wgd-modular/utf-8-samplified/firmware/mattel/mattel.h

const uint8_t BD[923] PROGMEM =          //BD_Samples:923
{
128,125,124,125,122,122,121,121,115,142,193,202,205,209,211,215,217,221,224,228,230,230,230,229,228,228,226,228,219,192,166,142,119,101,83,68,57,48,38,33,28,25,21,21,20,19,18,18,14,11,9,5,0,0,0,0,0,0,2,5,6,6,7,9,10,11,11,11,11,11,11,13,13,13,13,13,11,13,10,11,11,10,9,10,10,9,10,9,9,9,10,9,10,10,10,10,10,11,14,20,28,33,40,48,55,63,71,76,82,86,90,92,97,100,102,105,109,112,116,120,124,130,134,138,144,151,156,161,167,173,178,185,190,196,201,206,212,217,223,228,233,236,241,247,250,254,254,254,254,254,254,254,254,254,254,254,254,254,254,254,254,254,254,254,254,254,254,254,254,254,254,254,254,254,254,254,254,254,254,254,254,254,254,254,254,254,254,254,254,254,254,254,254,254,254,254,254,253,252,252,250,248,247,247,244,244,243,241,241,239,239,238,231,226,221,216,211,206,201,196,191,186,181,176,171,166,161,156,152,148,143,139,135,130,128,122,119,115,111,107,103,100,97,93,91,87,85,82,78,77,73,71,68,66,63,61,58,57,53,50,49,47,44,42,40,39,37,33,31,30,28,28,25,24,20,20,19,18,15,14,14,13,11,10,9,9,7,6,6,6,5,5,5,4,4,4,2,2,4,4,4,5,5,6,6,7,9,10,11,11,14,16,16,18,20,21,23,25,26,29,31,34,34,38,39,42,44,45,48,50,52,54,55,59,62,62,66,67,68,71,71,73,76,78,78,81,82,83,86,87,88,90,92,92,95,95,97,98,100,102,101,102,105,106,106,109,109,110,111,112,114,115,116,116,117,120,121,121,122,122,124,125,128,128,128,129,129,130,133,132,134,135,137,137,139,139,140,140,142,143,144,144,145,147,148,148,149,149,152,153,153,154,154,154,157,157,158,158,159,159,159,161,161,161,162,162,163,164,164,164,164,164,166,166,166,166,166,167,167,167,167,167,167,168,168,168,167,168,168,167,168,167,167,167,167,167,167,166,167,168,167,166,167,167,167,167,167,166,167,167,167,167,166,167,167,167,167,166,168,168,168,168,168,168,168,168,169,169,171,169,171,169,169,172,172,171,171,171,171,171,171,171,171,172,171,171,171,171,172,169,171,169,169,169,168,168,168,168,169,168,167,167,166,167,166,166,164,166,164,163,163,163,162,162,162,159,159,159,158,158,158,157,157,156,157,154,154,154,153,152,153,153,152,151,151,151,149,149,149,148,148,148,147,148,147,147,145,145,144,144,144,144,143,142,142,142,140,140,140,139,138,139,138,137,134,135,134,134,133,133,132,130,129,129,128,128,125,128,125,124,122,122,121,121,120,120,119,119,115,116,115,115,114,111,111,110,110,109,109,107,107,106,106,106,105,105,103,103,102,102,101,102,101,100,100,100,100,98,98,100,98,97,98,97,97,97,97,97,97,97,97,97,97,97,97,97,97,97,97,97,97,96,98,96,98,96,97,96,96,97,96,96,96,97,96,97,97,97,97,96,97,97,97,96,96,96,97,97,97,97,97,98,97,97,98,97,97,98,97,98,98,98,98,100,100,100,100,101,102,102,101,102,101,103,103,103,103,105,106,106,107,107,109,110,111,110,111,111,112,114,115,115,115,115,117,116,119,119,120,120,120,121,121,122,121,124,124,124,124,125,125,125,128,125,128,128,129,129,128,128,128,129,130,130,130,130,130,132,130,132,133,132,132,133,132,133,133,133,133,134,134,133,134,134,135,135,134,135,135,135,137,137,137,138,138,138,138,138,138,140,140,139,140,140,142,142,142,142,142,143,144,144,144,144,144,145,144,147,145,145,147,145,145,145,145,145,147,147,147,145,147,145,145,145,147,145,145,144,144,145,144,144,143,144,142,143,143,142,142,142,142,142,142,140,140,139,139,138,139,137,138,138,138,138,137,137,137,137,137,137,135,135,135,135,135,134,134,134,133,134,134,134,134,134,134,134,133,134,133,133,134,133,134,133,134,133,133,132,133,133,132,133,132,132,132,132,130,130,130,130,129,129,130,129,129,129,128,128,128,128,128,125,125,
};

const uint8_t SD[1824] PROGMEM =          //SD_SAMPLES:1824
{
128,132,128,132,132,132,128,142,103,4,34,0,9,29,49,49,73,78,108,98,128,128,128,167,147,157,157,211,177,162,142,226,152,172,137,182,172,132,162,152,216,172,147,73,152,108,98,201,123,147,123,118,182,147,152,93,103,211,73,172,152,132,201,172,192,152,157,147,113,103,157,73,147,128,128,157,73,123,132,132,108,137,142,123,201,103,167,113,152,162,142,137,137,177,128,88,118,157,83,98,108,128,78,162,118,123,78,83,157,93,167,68,64,132,88,93,88,147,128,132,14,177,98,54,172,64,162,142,128,113,147,152,44,123,103,68,162,108,64,118,113,118,118,113,128,118,78,98,128,73,113,73,142,93,162,108,93,64,73,137,59,88,73,132,88,147,108,118,172,103,142,88,167,88,113,142,128,142,128,123,103,73,108,132,108,103,44,157,93,54,167,83,157,128,98,157,137,137,118,167,152,68,98,162,34,206,113,103,128,132,167,157,172,78,108,162,98,147,113,103,177,68,182,128,187,132,98,108,123,118,142,113,113,167,118,167,152,113,172,128,78,187,123,137,147,147,162,157,157,128,152,132,147,132,177,152,137,88,152,118,98,172,113,162,108,147,137,157,118,132,137,128,103,157,59,157,167,68,177,98,177,172,167,113,118,172,108,128,147,137,162,137,123,147,132,132,142,128,147,132,123,132,157,132,123,118,152,113,93,137,103,108,142,113,108,152,147,123,128,128,152,113,177,128,137,128,142,103,123,167,93,132,142,147,128,98,142,137,108,142,103,172,137,113,118,152,128,132,142,132,142,123,132,132,123,142,128,128,132,147,137,142,123,128,128,132,157,142,132,118,108,93,128,113,108,147,98,123,128,123,128,128,152,118,152,123,162,113,137,167,142,128,152,142,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
};

const uint8_t HT[2424] PROGMEM =          //HT_SAMPLES:2424
{
129,128,132,132,135,133,135,133,136,131,142,107,35,22,6,2,0,5,10,21,34,54,74,95,116,138,158,177,194,209,218,224,228,229,228,225,220,215,206,197,185,172,160,147,136,125,114,106,100,95,93,92,96,105,115,128,142,156,171,185,198,209,215,218,220,220,217,214,208,202,193,183,171,158,144,132,120,109,99,91,84,77,73,72,75,84,92,104,116,130,143,155,167,175,180,183,183,183,178,174,168,160,152,140,128,115,102,89,78,68,59,51,44,41,38,36,38,46,55,66,79,92,104,117,130,142,150,156,159,161,159,157,153,148,142,135,125,115,103,93,83,73,64,58,51,47,44,42,43,43,49,59,70,83,96,110,124,136,148,159,168,172,176,176,175,171,166,160,153,146,137,126,115,105,94,85,77,71,65,61,58,57,57,58,62,71,81,93,106,120,132,146,158,169,179,186,190,192,191,189,185,180,174,167,159,150,138,128,119,109,102,95,88,84,80,79,79,79,80,86,94,105,116,129,141,153,166,176,187,196,202,205,205,205,201,196,191,184,176,167,157,146,136,124,115,107,99,92,87,82,80,79,79,80,82,87,97,107,118,131,142,153,165,175,184,192,197,200,200,198,195,190,185,177,170,161,151,141,131,121,112,104,97,92,87,84,82,82,81,82,85,89,98,108,118,129,141,152,161,171,180,187,193,196,196,195,191,187,180,173,166,158,148,138,127,118,109,101,94,87,81,78,75,75,74,74,76,78,83,91,100,111,121,131,142,152,161,168,176,182,185,186,185,183,177,173,166,159,153,144,134,125,115,107,100,93,87,83,79,77,76,76,77,78,81,84,91,99,109,120,130,140,149,158,166,174,180,185,187,187,185,182,177,171,166,158,151,142,134,124,115,107,100,93,88,84,81,79,78,78,79,81,82,84,90,98,106,115,125,136,144,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
,128,128,128,128,127,128,128,128,129,128,128,129,127,128,128,129,128,128,129,128,128,129,128,129,128,129,128,128,128,128,129,128,128,127,127,129,128,128,128,129,129,128,128,128,127,129,127,127,128,128,128,127,128,128,128,128,128,128,128,128,127,128,128,128,128,128,128,128,128,128,129,128,128,129,128,129,128,128,128,128,129,128,128,128,128,128,128,128,128,128,128,129,128,127,128,128,128,128,128,127,127,128,128,128,128,128,128,128,129,128,128,128,128,
};

const uint8_t HT3[2885] PROGMEM =          //HT3_SAMPLES:2885
{
128,123,118,114,109,104,100,95,91,86,82,76,76,85,96,108,122,135,152,168,185,201,215,230,243,250,255,255,255,253,251,246,241,234,229,223,216,210,205,200,196,192,189,188,187,187,187,187,188,188,189,190,191,189,188,186,182,179,174,170,164,159,153,147,140,134,127,122,116,111,105,101,97,94,92,88,86,84,83,83,81,82,81,81,81,80,80,79,79,77,77,77,78,80,82,86,90,94,98,102,105,109,114,117,119,123,126,128,131,133,136,138,138,141,142,143,144,144,145,145,145,144,144,143,140,138,136,134,131,128,126,123,121,118,116,113,110,109,107,104,102,101,98,97,95,94,91,88,86,83,80,78,74,72,70,67,64,63,61,59,59,57,55,54,54,53,53,52,53,53,53,55,54,55,57,58,58,61,63,63,66,67,69,70,73,76,77,79,80,83,86,89,94,100,104,111,117,122,129,134,141,146,152,157,162,167,172,176,179,184,187,190,192,195,197,200,202,203,204,205,206,207,206,206,206,205,204,201,200,197,195,193,191,189,186,184,181,179,176,174,171,169,166,163,162,160,157,153,150,147,144,141,136,133,130,126,125,121,118,115,113,110,110,108,105,103,103,101,100,99,98,97,97,97,96,95,95,95,94,95,94,94,94,94,94,95,95,95,96,96,96,97,98,99,99,101,103,107,110,115,119,123,127,132,137,141,144,148,153,157,160,164,167,169,172,175,177,179,181,183,184,186,188,189,190,191,191,193,193,193,193,193,192,192,190,188,187,186,184,181,179,176,175,171,169,166,163,160,157,155,151,147,145,141,137,134,130,125,122,118,114,111,107,105,101,99,95,93,90,88,86,84,83,80,78,78,75,74,73,72,72,71,70,70,69,69,69,68,70,69,70,70,70,71,72,72,73,75,77,77,80,81,83,83,85,89,92,96,101,105,111,116,121,126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
};

const uint8_t LT[1921] PROGMEM =          //LT_SAMPLES:1921
{
128,128,128,128,127,129,129,128,128,128,128,127,129,128,128,128,128,127,128,128,128,128,128,128,127,128,128,128,128,128,128,128,127,128,128,128,128,128,128,128,128,128,127,128,127,127,126,126,126,126,126,126,125,125,125,126,126,125,125,125,126,126,127,127,126,128,127,128,128,129,129,129,129,129,131,130,130,131,131,131,131,131,132,131,131,131,131,131,130,130,130,130,130,129,129,129,128,127,127,127,126,127,127,126,126,125,125,125,125,125,124,124,124,123,123,123,122,123,123,122,123,122,123,122,122,122,123,123,124,124,124,125,126,126,127,128,129,130,131,131,132,133,134,135,135,136,137,137,138,139,138,139,139,140,140,140,139,139,139,139,137,137,137,136,135,135,134,133,130,130,130,130,130,130,128,128,125,123,121,119,118,118,117,118,118,118,118,118,116,115,113,112,111,110,111,111,111,112,113,114,114,114,114,114,114,115,116,119,120,122,124,125,126,127,127,129,129,133,136,140,143,148,148,150,145,142,132,127,66,29,17,3,3,5,18,31,52,72,94,113,131,142,152,157,161,161,161,158,156,154,151,148,142,138,133,127,123,118,121,125,135,146,156,168,181,193,205,216,227,238,247,253,255,255,253,249,243,235,228,219,211,202,193,185,176,168,161,155,147,139,129,119,110,102,94,89,83,79,76,73,71,71,71,71,72,74,80,91,102,115,129,142,154,166,177,187,196,202,209,212,210,206,199,190,182,171,161,151,141,131,123,113,106,99,92,87,82,76,69,62,55,48,42,38,33,29,27,24,22,22,21,20,21,21,21,22,28,36,47,57,69,81,93,106,116,127,138,146,154,163,169,173,174,173,169,166,161,155,149,144,137,133,127,122,118,115,112,110,107,10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
};
