wgd-modular/utf-8-samplified/firmware/cavetechno/CH.h

#ifndef CH_H_
#define CH_H_
 
const uint16_t CHLen = 2347;

const uint8_t CH[2347] PROGMEM = {130, 125, 131, 125, 131, 128, 129, 120, 137,
120, 143, 112, 150, 109, 135, 159, 14, 190, 124, 104, 151, 158, 108, 147, 108,
162, 201, 82, 166, 103, 77, 75, 134, 67, 157, 85, 123, 183, 131, 191, 169, 174,
140, 154, 93, 163, 53, 89, 79, 55, 103, 106, 142, 145, 185, 123, 225, 156, 170,
180, 132, 112, 83, 57, 96, 94, 40, 150, 84, 135, 167, 171, 182, 191, 143, 170,
168, 70, 149, 87, 63, 75, 83, 89, 142, 116, 149, 188, 134, 182, 180, 161, 136,
136, 93, 106, 70, 92, 113, 76, 114, 127, 151, 152, 170, 161, 176, 133, 148, 144,
106, 117, 93, 93, 87, 95, 114, 152, 109, 147, 164, 143, 167, 152, 145, 145, 118,
98, 139, 82, 101, 116, 96, 116, 129, 136, 156, 155, 125, 171, 139, 135, 145,
127, 118, 108, 94, 113, 117, 100, 135, 123, 131, 138, 149, 152, 142, 136, 145,
133, 117, 129, 114, 116, 103, 108, 125, 122, 124, 147, 134, 123, 147, 138, 146,
137, 127, 132, 126, 102, 126, 128, 102, 130, 118, 126, 134, 126, 139, 144, 123,
140, 146, 127, 133, 123, 124, 116, 114, 120, 132, 118, 122, 129, 128, 133, 132,
146, 136, 131, 131, 136, 122, 123, 122, 121, 123, 112, 127, 132, 122, 123, 139,
125, 138, 137, 134, 141, 121, 125, 133, 119, 118, 133, 118, 120, 119, 124, 136,
128, 130, 141, 136, 128, 139, 131, 129, 121, 122, 127, 118, 119, 127, 125, 119,
130, 133, 139, 132, 134, 139, 128, 123, 130, 128, 122, 121, 118, 126, 119, 122,
135, 131, 127, 137, 135, 134, 134, 125, 134, 123, 119, 127, 125, 119, 124, 123,
126, 131, 127, 140, 134, 130, 132, 133, 126, 129, 125, 125, 123, 115, 127, 125,
125, 125, 134, 129, 136, 133, 136, 134, 121, 132, 128, 123, 123, 127, 122, 124,
118, 130, 133, 126, 134, 135, 131, 128, 134, 129, 133, 121, 127, 129, 119, 123,
127, 126, 123, 129, 129, 136, 128, 130, 134, 130, 126, 133, 130, 127, 125, 120,
129, 118, 125, 130, 127, 127, 130, 130, 132, 133, 129, 137, 127, 128, 129, 128,
122, 124, 123, 123, 126, 125, 132, 128, 128, 130, 135, 130, 134, 132, 131, 128,
120, 128, 123, 122, 124, 127, 123, 128, 127, 134, 132, 127, 135, 133, 129, 128,
130, 123, 125, 120, 128, 126, 123, 130, 129, 128, 128, 134, 132, 134, 126, 132,
128, 123, 126, 127, 125, 124, 126, 126, 132, 125, 132, 131, 128, 129, 132, 130,
128, 126, 125, 129, 121, 128, 129, 128, 125, 129, 127, 130, 129, 130, 134, 125,
129, 128, 128, 125, 127, 127, 128, 124, 127, 131, 125, 128, 128, 132, 128, 130,
129, 132, 126, 125, 130, 127, 126, 127, 129, 124, 125, 125, 131, 128, 127, 130,
131, 129, 128, 132, 128, 129, 125, 130, 126, 125, 127, 127, 126, 125, 129, 129,
130, 127, 132, 129, 128, 128, 131, 129, 127, 128, 125, 127, 123, 127, 127, 126,
127, 130, 130, 129, 130, 131, 132, 127, 130, 129, 127, 124, 126, 124, 124, 125,
127, 131, 126, 130, 131, 132, 129, 132, 131, 131, 125, 125, 127, 123, 124, 124,
127, 125, 129, 129, 133, 129, 131, 133, 131, 130, 128, 129, 124, 124, 122, 126,
124, 126, 128, 129, 129, 130, 133, 131, 132, 129, 132, 126, 126, 124, 125, 123,
123, 126, 127, 128, 128, 133, 130, 131, 131, 133, 130, 128, 127, 126, 124, 122,
126, 125, 126, 126, 130, 129, 130, 130, 132, 131, 129, 131, 128, 127, 124, 126,
126, 125, 125, 129, 128, 127, 129, 129, 131, 129, 130, 131, 130, 126, 128, 127,
125, 126, 126, 127, 126, 127, 129, 129, 127, 129, 131, 130, 130, 129, 129, 127,
126, 127, 127, 125, 127, 128, 127, 127, 127, 130, 130, 129, 130, 131, 127, 128,
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

#endif /* CH_H_ */
