wgd-modular/utf-8-samplified/firmware/cavetechno/CL.h

#ifndef CL_H_
#define CL_H_
 
const uint16_t CLLen = 2447;

const uint8_t CL[2447] PROGMEM = {128, 127, 128, 127, 128, 128, 128, 128, 128,
128, 127, 129, 127, 129, 125, 128, 125, 117, 126, 120, 138, 145, 122, 168, 167,
112, 88, 126, 138, 168, 156, 131, 111, 135, 168, 116, 171, 134, 49, 77, 177, 84,
89, 188, 175, 172, 140, 121, 114, 104, 74, 108, 117, 137, 154, 149, 132, 130,
134, 138, 135, 138, 128, 109, 98, 104, 130, 122, 104, 124, 133, 117, 149, 161,
158, 124, 121, 141, 123, 109, 124, 119, 107, 113, 127, 126, 138, 153, 126, 164,
157, 144, 112, 97, 121, 106, 111, 90, 103, 143, 144, 155, 169, 149, 136, 114,
101, 120, 112, 117, 123, 119, 133, 135, 152, 149, 146, 118, 113, 116, 114, 132,
121, 120, 119, 122, 126, 140, 141, 149, 146, 127, 116, 127, 133, 127, 105, 105,
102, 123, 143, 129, 141, 125, 137, 158, 145, 136, 143, 107, 85, 98, 122, 130,
141, 139, 148, 144, 126, 105, 133, 180, 67, 164, 179, 98, 153, 123, 108, 124,
146, 125, 119, 152, 114, 75, 170, 152, 94, 135, 142, 113, 128, 114, 133, 137,
112, 149, 144, 140, 132, 101, 118, 129, 91, 163, 103, 122, 160, 121, 146, 115,
116, 111, 133, 139, 154, 114, 106, 131, 167, 154, 129, 126, 68, 90, 106, 130,
175, 153, 139, 139, 131, 118, 99, 99, 111, 151, 159, 134, 97, 106, 122, 150,
159, 151, 154, 94, 92, 142, 156, 91, 102, 140, 107, 130, 143, 154, 146, 108, 97,
114, 143, 143, 153, 156, 134, 98, 100, 97, 112, 148, 131, 137, 136, 138, 131,
129, 129, 116, 127, 127, 136, 146, 126, 101, 108, 129, 143, 159, 137, 120, 108,
91, 137, 147, 131, 97, 130, 157, 114, 139, 127, 124, 148, 121, 130, 118, 93,
143, 141, 123, 120, 119, 131, 131, 133, 149, 129, 101, 113, 150, 138, 132, 141,
115, 77, 108, 146, 113, 166, 169, 115, 89, 135, 148, 135, 134, 115, 108, 125,
147, 116, 118, 142, 96, 124, 163, 117, 86, 175, 166, 78, 172, 118, 80, 169, 155,
46, 117, 164, 99, 162, 172, 93, 90, 156, 164, 134, 118, 134, 112, 106, 101, 125,
128, 124, 168, 179, 129, 80, 111, 157, 156, 109, 99, 112, 111, 121, 152, 158,
137, 122, 108, 125, 125, 123, 146, 139, 117, 130, 123, 94, 129, 152, 142, 145,
143, 109, 95, 125, 143, 145, 124, 140, 125, 122, 107, 94, 123, 125, 184, 150,
130, 126, 75, 94, 153, 179, 107, 102, 153, 130, 112, 108, 149, 162, 115, 129,
126, 89, 110, 130, 129, 133, 136, 170, 151, 122, 97, 93, 138, 123, 112, 133,
130, 140, 150, 135, 124, 137, 140, 106, 88, 114, 160, 128, 111, 151, 136, 122,
144, 113, 102, 156, 156, 122, 88, 107, 124, 125, 145, 153, 155, 129, 108, 140,
113, 103, 133, 112, 152, 125, 91, 164, 133, 125, 154, 102, 117, 135, 149, 109,
88, 132, 171, 156, 91, 147, 166, 106, 107, 77, 117, 167, 105, 152, 144, 91, 128,
158, 146, 142, 123, 94, 108, 119, 143, 159, 172, 132, 97, 103, 98, 115, 151,
157, 100, 96, 124, 157, 167, 115, 83, 112, 160, 171, 140, 122, 125, 89, 124,
136, 124, 139, 147, 124, 92, 117, 132, 140, 152, 146, 109, 126, 133, 123, 136,
110, 88, 116, 162, 160, 142, 135, 99, 94, 94, 135, 159, 158, 142, 96, 140, 146,
108, 98, 130, 148, 115, 109, 140, 166, 130, 106, 86, 107, 158, 158, 157, 129,
101, 90, 137, 168, 136, 87, 109, 133, 131, 134, 114, 135, 162, 164, 113, 89,
103, 136, 163, 154, 117, 76, 83, 118, 188, 178, 118, 103, 129, 164, 108, 100,
123, 130, 123, 136, 150, 118, 114, 143, 147, 104, 139, 142, 100, 122, 146, 114,
103, 170, 161, 99, 92, 118, 145, 141, 142, 132, 133, 144, 92, 103, 136, 136, 95,
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

#endif /* CL_H_ */
