wgd-modular/utf-8-samplified/firmware/dilectro/BD.h

#ifndef BD_H_
#define BD_H_
 
const uint16_t BDLen = 3332;

const uint8_t BD[3332] PROGMEM = {128, 128, 128, 58, 58, 82, 84, 85, 72, 62, 50,
42, 42, 61, 56, 56, 55, 60, 68, 79, 90, 102, 114, 126, 139, 150, 162, 172, 183,
192, 201, 209, 218, 225, 233, 238, 244, 247, 250, 252, 253, 253, 252, 251, 248,
245, 242, 238, 232, 227, 220, 212, 203, 194, 184, 173, 162, 150, 139, 130, 121,
114, 107, 101, 95, 90, 85, 81, 77, 73, 69, 66, 63, 60, 58, 56, 54, 52, 50, 49,
48, 47, 46, 45, 45, 45, 44, 44, 44, 44, 44, 45, 45, 46, 47, 48, 49, 50, 51, 53,
54, 56, 58, 59, 61, 64, 66, 68, 70, 73, 76, 78, 81, 84, 87, 90, 94, 97, 101,
105, 109, 113, 117, 121, 126, 130, 135, 139, 144, 149, 154, 158, 163, 168, 173,
178, 182, 187, 191, 196, 200, 204, 208, 212, 216, 220, 223, 226, 229, 232, 234,
236, 238, 240, 241, 243, 243, 244, 244, 244, 243, 243, 242, 241, 239, 237, 236,
234, 231, 229, 226, 223, 220, 217, 214, 211, 207, 204, 200, 196, 193, 189, 185,
181, 177, 173, 169, 165, 160, 156, 152, 148, 144, 140, 136, 131, 127, 123, 119,
115, 111, 108, 104, 100, 96, 93, 89, 86, 82, 79, 76, 73, 70, 67, 64, 61, 58, 56,
53, 51, 48, 46, 44, 42, 40, 38, 37, 35, 34, 32, 31, 30, 29, 28, 28, 27, 27, 26,
26, 26, 26, 26, 26, 27, 27, 28, 29, 29, 30, 32, 33, 34, 36, 37, 39, 40, 42, 44,
46, 48, 51, 53, 55, 58, 60, 63, 65, 68, 71, 74, 77, 80, 83, 86, 89, 92, 96, 99,
103, 106, 110, 113, 117, 121, 125, 129, 134, 138, 142, 147, 151, 155, 160, 164,
169, 173, 178, 182, 186, 191, 195, 199, 203, 207, 210, 214, 218, 221, 224, 227,
230, 233, 235, 237, 239, 241, 242, 243, 244, 245, 245, 245, 245, 244, 244, 243,
241, 240, 238, 236, 234, 231, 229, 226, 223, 220, 217, 214, 211, 207, 204, 200,
197, 193, 190, 186, 182, 178, 175, 171, 167, 163, 160, 156, 152, 148, 144, 141,
137, 133, 129, 126, 122, 119, 115, 112, 108, 105, 102, 98, 95, 92, 89, 86, 84,
81, 78, 76, 73, 71, 68, 66, 64, 62, 60, 58, 56, 55, 53, 52, 50, 49, 48, 47, 46,
45, 45, 44, 43, 43, 43, 43, 43, 43, 43, 43, 43, 44, 44, 45, 46, 47, 48, 49, 50,
51, 52, 54, 55, 57, 58, 60, 62, 64, 66, 68, 70, 72, 74, 76, 78, 80, 82, 85, 87,
89, 92, 94, 97, 99, 102, 105, 107, 110, 113, 115, 118, 121, 123, 126, 129, 132,
134, 137, 140, 143, 146, 149, 152, 155, 157, 160, 163, 166, 169, 172, 174, 177,
180, 182, 185, 187, 190, 192, 194, 196, 198, 200, 202, 203, 205, 206, 207, 208,
209, 210, 210, 211, 211, 211, 211, 210, 210, 209, 208, 207, 206, 205, 204, 202,
201, 199, 197, 196, 194, 192, 190, 188, 186, 184, 181, 179, 177, 175, 172, 170,
168, 165, 163, 161, 158, 156, 153, 151, 149, 146, 144, 141, 139, 136, 134, 132,
129, 127, 125, 122, 120, 118, 116, 114, 111, 109, 107, 105, 104, 102, 100, 98,
96, 95, 93, 91, 90, 88, 87, 85, 84, 83, 82, 81, 80, 79, 78, 77, 76, 75, 75, 74,
74, 73, 73, 72, 72, 72, 72, 72, 72, 72, 72, 72, 73, 73, 74, 74, 75, 75, 76, 77,
78, 79, 79, 80, 81, 83, 84, 85, 86, 87, 89, 90, 91, 93, 94, 96, 97, 99, 100,
102, 104, 105, 107, 109, 110, 112, 114, 116, 117, 119, 121, 123, 124, 126, 128,
130, 132, 133, 135, 137, 139, 140, 142, 144, 146, 147, 149, 151, 153, 154, 156,
158, 159, 161, 162, 164, 165, 167, 168, 170, 171, 172, 173, 174, 176, 176, 177,
178, 179, 180, 180, 181, 181, 181, 181, 182, 182, 182, 181, 181, 181, 180, 180,
179, 178, 178, 177, 176, 175, 174, 173, 172, 170, 169, 168, 167, 166, 164, 163,
162, 160, 159, 157, 156, 154, 153, 151, 150, 148, 147, 145, 144, 142, 140, 139,
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

#endif /* BD_H_ */
