wgd-modular/utf-8-samplified/firmware/dilectro/CR.h

#ifndef CR_H_
#define CR_H_
 
const uint16_t CRLen = 7156;

const uint8_t CR[7156] PROGMEM = {128, 127, 125, 125, 125, 122, 120, 119, 121,
120, 116, 116, 120, 125, 133, 140, 147, 152, 157, 158, 166, 215, 223, 186, 149,
110, 78, 52, 36, 30, 30, 34, 49, 74, 103, 135, 160, 179, 194, 206, 210, 216,
233, 215, 185, 153, 120, 91, 67, 52, 43, 42, 42, 77, 106, 117, 133, 145, 159,
167, 174, 174, 175, 190, 180, 158, 137, 116, 95, 76, 66, 64, 69, 74, 86, 103,
124, 145, 163, 177, 186, 189, 186, 179, 185, 189, 165, 134, 106, 82, 66, 56, 54,
59, 66, 79, 97, 117, 137, 155, 167, 174, 178, 178, 175, 178, 170, 153, 136, 119,
106, 95, 89, 86, 88, 90, 100, 119, 127, 134, 141, 146, 149, 150, 150, 148, 151,
149, 139, 130, 121, 113, 105, 101, 100, 102, 105, 110, 118, 127, 135, 143, 150,
154, 155, 154, 151, 152, 154, 146, 132, 119, 107, 98, 93, 92, 93, 97, 103, 112,
122, 133, 143, 149, 154, 156, 157, 155, 157, 153, 143, 133, 123, 114, 107, 103,
101, 102, 103, 109, 122, 128, 133, 137, 141, 143, 144, 144, 142, 144, 142, 136,
129, 123, 117, 112, 109, 108, 110, 112, 116, 121, 127, 133, 139, 143, 146, 147,
146, 144, 145, 146, 140, 131, 121, 113, 107, 104, 103, 104, 106, 111, 117, 124,
131, 138, 143, 145, 147, 147, 146, 147, 145, 138, 131, 124, 119, 114, 111, 110,
111, 111, 116, 124, 128, 131, 134, 136, 138, 138, 138, 137, 138, 137, 133, 129,
125, 121, 118, 116, 116, 117, 118, 120, 124, 127, 131, 135, 138, 140, 141, 140,
139, 139, 140, 136, 130, 123, 118, 114, 111, 110, 111, 113, 116, 120, 125, 130,
135, 139, 141, 142, 143, 142, 143, 141, 135, 130, 125, 121, 117, 115, 113, 114,
114, 118, 125, 128, 131, 133, 135, 136, 137, 137, 136, 137, 136, 132, 129, 125,
122, 118, 117, 116, 117, 118, 121, 124, 128, 131, 135, 138, 139, 140, 140, 138,
139, 140, 136, 130, 123, 118, 114, 112, 111, 112, 113, 116, 120, 125, 130, 135,
138, 141, 142, 142, 141, 142, 140, 135, 130, 125, 121, 117, 115, 114, 114, 115,
118, 125, 128, 131, 133, 135, 136, 137, 137, 136, 137, 136, 132, 129, 125, 122,
119, 117, 117, 117, 119, 121, 124, 128, 131, 135, 137, 139, 140, 139, 138, 139,
139, 136, 129, 124, 118, 115, 112, 111, 112, 114, 117, 121, 125, 130, 135, 138,
140, 141, 142, 141, 142, 140, 135, 130, 125, 121, 118, 115, 114, 115, 115, 119,
125, 128, 131, 133, 135, 136, 136, 136, 135, 137, 136, 132, 129, 125, 122, 119,
117, 117, 118, 119, 121, 124, 128, 131, 134, 137, 139, 139, 139, 138, 138, 139,
135, 129, 124, 119, 115, 113, 112, 113, 114, 117, 121, 125, 130, 135, 138, 140,
141, 141, 140, 141, 139, 135, 130, 125, 121, 118, 116, 115, 115, 116, 119, 125,
128, 130, 133, 134, 136, 136, 136, 135, 136, 135, 132, 129, 125, 122, 119, 118,
117, 118, 119, 121, 124, 128, 131, 134, 137, 138, 139, 139, 137, 138, 138, 135,
129, 124, 119, 115, 113, 113, 113, 115, 117, 121, 126, 130, 135, 137, 139, 141,
141, 140, 141, 139, 134, 130, 125, 122, 118, 116, 115, 116, 116, 119, 125, 128,
130, 132, 134, 135, 136, 136, 135, 136, 135, 132, 128, 125, 122, 120, 118, 118,
119, 120, 122, 124, 128, 131, 134, 136, 138, 139, 138, 137, 137, 138, 135, 129,
124, 119, 116, 114, 113, 114, 115, 118, 121, 126, 130, 134, 137, 139, 140, 140,
140, 140, 139, 134, 130, 125, 122, 118, 117, 116, 116, 117, 120, 125, 128, 130,
132, 134, 135, 136, 135, 135, 136, 135, 132, 128, 125, 123, 120, 118, 118, 119,
120, 122, 125, 128, 131, 134, 136, 138, 138, 138, 137, 137, 138, 135, 129, 124,
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

#endif /* CR_H_ */
