wgd-modular/utf-8-samplified/firmware/dilectro/OH.h

#ifndef OH_H_
#define OH_H_
 
const uint16_t OHLen = 3035;

const uint8_t OH[3035] PROGMEM = {129, 127, 129, 127, 129, 136, 125, 130, 125,
134, 122, 129, 126, 137, 116, 137, 127, 118, 141, 122, 130, 127, 131, 123, 133,
126, 132, 122, 138, 118, 133, 129, 130, 125, 124, 137, 119, 138, 121, 134, 123,
131, 125, 131, 130, 127, 121, 135, 131, 128, 129, 135, 131, 126, 144, 122, 135,
127, 133, 118, 135, 128, 119, 136, 126, 120, 138, 122, 126, 140, 124, 143, 124,
136, 117, 142, 124, 117, 135, 123, 121, 129, 128, 117, 133, 121, 134, 119, 129,
125, 137, 123, 133, 120, 131, 127, 118, 136, 112, 142, 117, 131, 128, 122, 128,
126, 122, 135, 119, 124, 123, 131, 126, 117, 142, 121, 132, 121, 131, 120, 135,
128, 120, 133, 121, 127, 129, 128, 126, 125, 133, 123, 132, 128, 123, 132, 120,
136, 123, 132, 129, 131, 132, 125, 128, 131, 125, 133, 117, 133, 134, 120, 136,
123, 128, 126, 126, 126, 130, 128, 132, 122, 141, 123, 134, 126, 130, 125, 129,
124, 128, 132, 120, 136, 121, 133, 121, 131, 125, 131, 119, 135, 115, 139, 124,
140, 118, 132, 129, 113, 142, 114, 137, 112, 141, 114, 137, 125, 132, 125, 131,
124, 133, 126, 127, 135, 117, 134, 123, 137, 119, 133, 122, 134, 118, 136, 123,
133, 126, 127, 131, 127, 129, 127, 128, 125, 134, 120, 134, 122, 132, 121, 134,
125, 129, 130, 129, 129, 128, 130, 126, 132, 126, 130, 127, 127, 129, 130, 124,
129, 126, 131, 126, 128, 127, 131, 126, 129, 126, 128, 131, 119, 138, 124, 126,
134, 124, 132, 127, 127, 128, 126, 131, 124, 129, 128, 128, 126, 127, 125, 134,
126, 129, 125, 129, 131, 125, 130, 125, 136, 117, 135, 126, 132, 126, 129, 127,
129, 128, 124, 136, 122, 132, 126, 134, 123, 133, 124, 132, 122, 137, 127, 125,
137, 118, 139, 118, 137, 126, 127, 132, 126, 129, 131, 125, 133, 124, 133, 130,
119, 137, 124, 134, 123, 133, 123, 133, 127, 126, 132, 125, 132, 128, 129, 128,
128, 129, 127, 128, 132, 120, 137, 124, 130, 126, 132, 129, 126, 133, 124, 130,
128, 130, 127, 130, 125, 133, 120, 135, 122, 133, 127, 127, 129, 126, 134, 124,
132, 127, 130, 125, 134, 122, 134, 126, 126, 129, 133, 122, 132, 130, 123, 130,
127, 133, 124, 131, 127, 127, 131, 127, 130, 129, 123, 133, 125, 132, 126, 131,
126, 129, 126, 131, 130, 125, 132, 127, 127, 128, 129, 127, 127, 129, 131, 121,
136, 123, 131, 127, 129, 127, 130, 127, 130, 126, 130, 129, 124, 134, 122, 132,
124, 131, 125, 130, 126, 130, 127, 128, 125, 133, 125, 128, 127, 128, 128, 123,
134, 124, 131, 124, 132, 125, 130, 127, 130, 124, 131, 126, 127, 130, 127, 128,
128, 128, 125, 134, 123, 132, 125, 131, 127, 129, 128, 127, 129, 128, 127, 128,
129, 126, 130, 128, 128, 128, 128, 128, 128, 126, 131, 124, 129, 128, 127, 128,
129, 128, 128, 128, 128, 128, 126, 131, 124, 131, 126, 127, 130, 125, 129, 127,
128, 129, 124, 131, 126, 127, 129, 126, 130, 126, 130, 126, 129, 128, 126, 129,
127, 127, 127, 129, 128, 124, 130, 128, 126, 128, 129, 126, 129, 128, 124, 132,
126, 129, 127, 128, 129, 126, 129, 127, 127, 130, 125, 128, 131, 123, 132, 124,
131, 126, 127, 129, 127, 129, 126, 129, 127, 130, 125, 130, 124, 133, 125, 128,
128, 129, 126, 130, 127, 124, 133, 123, 131, 127, 128, 126, 131, 125, 130, 128,
130, 125, 130, 129, 126, 128, 128, 128, 126, 132, 123, 134, 125, 129, 128, 127,
128, 127, 127, 131, 125, 127, 129, 128, 128, 128, 129, 126, 131, 126, 129, 126,
130, 125, 130, 128, 129, 126, 130, 126, 128, 130, 126, 128, 127, 130, 125, 131,
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

#endif /* OH_H_ */
