wgd-modular/utf-8-samplified/firmware/dilectro/RD.h

#ifndef RD_H_
#define RD_H_
 
const uint16_t RDLen = 4867;

const uint8_t RD[4867] PROGMEM = {127, 129, 127, 129, 127, 129, 126, 130, 126,
130, 125, 133, 118, 37, 36, 50, 55, 65, 64, 61, 54, 55, 59, 76, 77, 111, 199,
233, 241, 239, 227, 224, 218, 219, 217, 217, 215, 215, 212, 210, 207, 204, 201,
199, 197, 195, 194, 193, 192, 192, 192, 182, 167, 153, 140, 127, 115, 103, 91,
79, 70, 57, 44, 34, 22, 21, 26, 30, 33, 35, 37, 39, 40, 42, 44, 46, 49, 51, 53,
56, 57, 59, 59, 60, 69, 80, 89, 98, 106, 115, 124, 132, 140, 146, 155, 163, 170,
177, 182, 188, 193, 197, 201, 205, 208, 212, 214, 212, 209, 206, 204, 203, 201,
199, 198, 196, 192, 188, 183, 179, 174, 169, 163, 157, 151, 144, 138, 131, 123,
115, 108, 100, 93, 88, 81, 74, 69, 63, 59, 55, 52, 49, 47, 47, 50, 52, 54, 56,
58, 59, 60, 62, 67, 72, 77, 82, 87, 93, 98, 103, 109, 115, 120, 126, 132, 138,
142, 146, 153, 157, 162, 166, 170, 174, 178, 181, 184, 186, 189, 190, 192, 193,
193, 193, 194, 193, 194, 189, 182, 179, 176, 174, 171, 168, 164, 160, 156, 151,
146, 142, 137, 131, 126, 120, 115, 109, 104, 99, 95, 89, 84, 80, 77, 74, 71, 69,
67, 66, 66, 66, 66, 67, 69, 71, 73, 76, 78, 82, 85, 89, 93, 97, 102, 106, 110,
115, 120, 125, 129, 134, 138, 141, 146, 151, 154, 158, 161, 164, 167, 170, 172,
174, 176, 178, 179, 180, 180, 181, 180, 180, 180, 179, 177, 176, 174, 172, 170,
167, 164, 161, 157, 153, 150, 145, 141, 137, 132, 128, 123, 119, 114, 109, 105,
101, 98, 93, 89, 86, 83, 81, 79, 78, 76, 75, 75, 75, 76, 77, 78, 80, 82, 84, 86,
89, 92, 95, 99, 102, 106, 109, 113, 117, 121, 125, 128, 132, 136, 138, 143, 146,
149, 152, 155, 158, 160, 163, 165, 166, 168, 170, 171, 172, 172, 173, 173, 173,
172, 171, 170, 169, 168, 166, 165, 163, 160, 158, 155, 152, 149, 146, 142, 139,
136, 132, 128, 124, 120, 117, 113, 109, 106, 103, 101, 96, 94, 92, 90, 88, 86,
85, 84, 84, 84, 84, 84, 85, 86, 87, 89, 91, 93, 95, 97, 100, 103, 106, 109, 112,
115, 118, 121, 125, 128, 131, 134, 136, 141, 143, 146, 149, 151, 154, 156, 158,
160, 162, 163, 164, 165, 166, 167, 167, 167, 167, 167, 166, 166, 165, 164, 162,
161, 159, 157, 155, 152, 150, 147, 144, 141, 138, 135, 132, 129, 125, 122, 119,
116, 113, 110, 107, 105, 103, 99, 97, 95, 93, 92, 91, 90, 89, 89, 89, 89, 89,
90, 91, 92, 94, 95, 97, 99, 101, 103, 106, 108, 111, 114, 116, 119, 122, 125,
128, 131, 132, 135, 139, 141, 144, 146, 148, 150, 152, 154, 155, 157, 158, 159,
160, 161, 161, 162, 162, 162, 162, 161, 160, 160, 159, 158, 156, 155, 153, 151,
150, 148, 145, 143, 141, 138, 136, 133, 131, 128, 125, 123, 120, 118, 115, 113,
111, 108, 107, 105, 102, 101, 100, 98, 97, 97, 96, 96, 96, 96, 96, 96, 97, 98,
99, 100, 101, 103, 105, 106, 108, 110, 112, 114, 116, 118, 121, 123, 125, 128,
130, 131, 134, 137, 138, 141, 142, 144, 146, 147, 149, 150, 151, 153, 154, 154,
155, 156, 156, 156, 156, 156, 156, 155, 155, 154, 153, 152, 151, 150, 148, 147,
145, 143, 141, 140, 138, 136, 134, 132, 129, 127, 125, 123, 121, 119, 117, 115,
113, 111, 110, 109, 107, 105, 104, 103, 103, 102, 101, 101, 101, 101, 101, 102,
102, 103, 104, 105, 106, 107, 108, 110, 111, 113, 114, 116, 118, 120, 122, 124,
125, 127, 129, 130, 133, 135, 136, 138, 140, 141, 143, 144, 145, 146, 147, 148,
149, 150, 150, 151, 151, 151, 151, 151, 151, 151, 150, 150, 149, 148, 147, 146,
145, 144, 143, 141, 140, 139, 137, 135, 134, 132, 130, 129, 127, 125, 124, 122,
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

#endif /* RD_H_ */
