wgd-modular/utf-8-samplified/firmware/dilectro/SD.h

#ifndef SD_H_
#define SD_H_
 
const uint16_t SDLen = 2552;

const uint8_t SD[2552] PROGMEM = {129, 127, 129, 127, 128, 128, 129, 137, 154,
184, 192, 191, 176, 191, 99, 122, 170, 36, 31, 45, 45, 39, 53, 54, 63, 68, 72,
83, 80, 98, 82, 156, 145, 94, 106, 135, 125, 159, 178, 137, 110, 174, 248, 187,
162, 197, 231, 200, 217, 219, 204, 195, 199, 201, 189, 189, 170, 183, 170, 171,
157, 130, 107, 49, 131, 81, 32, 44, 64, 108, 48, 63, 63, 70, 81, 110, 101, 87,
130, 183, 126, 118, 137, 142, 165, 114, 186, 199, 137, 143, 198, 190, 168, 180,
148, 172, 201, 178, 166, 177, 155, 134, 151, 160, 130, 100, 81, 82, 83, 55, 51,
37, 43, 99, 90, 52, 33, 55, 56, 82, 76, 81, 165, 111, 136, 147, 121, 145, 141,
153, 155, 134, 166, 180, 161, 163, 159, 154, 167, 124, 157, 173, 136, 129, 90,
164, 155, 122, 98, 97, 90, 88, 69, 53, 110, 88, 39, 75, 86, 55, 57, 66, 69, 74,
95, 101, 97, 92, 147, 155, 123, 136, 124, 130, 201, 170, 129, 155, 179, 136,
155, 190, 173, 143, 126, 183, 158, 169, 144, 128, 137, 132, 106, 136, 148, 87,
102, 94, 122, 90, 90, 114, 71, 90, 111, 116, 94, 84, 126, 102, 107, 152, 127,
132, 137, 132, 139, 177, 168, 153, 129, 164, 197, 149, 155, 145, 142, 168, 160,
151, 142, 131, 159, 148, 118, 121, 140, 104, 100, 134, 122, 116, 95, 101, 100,
102, 100, 103, 101, 101, 126, 100, 123, 99, 131, 151, 132, 104, 150, 171, 139,
143, 122, 190, 142, 165, 162, 149, 138, 175, 153, 140, 154, 131, 167, 127, 136,
111, 144, 125, 124, 124, 100, 114, 112, 111, 99, 106, 85, 90, 140, 107, 69, 131,
113, 107, 95, 106, 144, 96, 142, 143, 126, 138, 135, 146, 143, 151, 149, 153,
152, 145, 137, 185, 151, 147, 138, 132, 156, 135, 150, 136, 135, 100, 135, 147,
117, 105, 98, 139, 127, 86, 119, 122, 107, 99, 110, 126, 105, 117, 109, 116,
129, 127, 131, 119, 141, 133, 118, 160, 138, 138, 150, 142, 146, 146, 148, 142,
148, 130, 135, 154, 138, 125, 124, 148, 125, 122, 136, 123, 124, 110, 112, 110,
130, 120, 104, 117, 99, 112, 139, 113, 115, 115, 109, 137, 121, 132, 134, 112,
147, 150, 131, 137, 138, 142, 144, 143, 147, 142, 149, 140, 150, 129, 130, 165,
151, 114, 134, 147, 126, 123, 105, 144, 131, 114, 121, 113, 123, 102, 121, 128,
97, 128, 124, 126, 101, 121, 127, 116, 129, 125, 138, 126, 124, 122, 154, 135,
135, 136, 137, 139, 144, 136, 125, 153, 145, 136, 147, 139, 131, 122, 129, 143,
124, 128, 115, 122, 138, 121, 121, 107, 125, 129, 102, 124, 133, 106, 111, 136,
122, 118, 123, 122, 128, 126, 131, 130, 133, 133, 135, 138, 125, 141, 156, 130,
130, 141, 139, 153, 126, 139, 145, 129, 132, 129, 130, 133, 119, 117, 151, 128,
118, 118, 120, 124, 118, 109, 128, 128, 113, 123, 107, 128, 127, 113, 138, 121,
126, 120, 129, 136, 122, 142, 118, 148, 132, 130, 153, 131, 135, 133, 136, 135,
135, 135, 133, 135, 123, 131, 148, 126, 128, 112, 133, 133, 119, 124, 117, 125,
109, 125, 126, 116, 128, 119, 125, 116, 125, 118, 116, 139, 127, 125, 120, 133,
122, 139, 134, 130, 137, 140, 137, 130, 129, 124, 150, 129, 140, 134, 122, 129,
148, 131, 127, 123, 119, 144, 124, 122, 118, 134, 125, 118, 117, 127, 125, 119,
131, 120, 109, 129, 136, 118, 125, 122, 129, 125, 131, 126, 134, 123, 125, 141,
137, 140, 123, 136, 140, 129, 135, 123, 129, 144, 130, 131, 119, 132, 141, 125,
117, 131, 130, 123, 133, 111, 126, 129, 112, 127, 130, 118, 123, 120, 119, 124,
131, 125, 125, 120, 118, 144, 126, 120, 133, 134, 132, 131, 121, 129, 147, 129,
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

#endif /* SD_H_ */
