wgd-modular/utf-8-samplified/firmware/jungle/BD.h

#ifndef BD_H_
#define BD_H_
 
const uint16_t BDLen = 3000; 
const uint8_t  BD[3000] PROGMEM = {128, 127, 128, 127, 128, 128, 128, 128, 128,
128, 119, 117, 118, 121, 119, 126, 131, 130, 129, 137, 132, 140, 142, 144, 137,
138, 145, 134, 138, 179, 207, 231, 255, 174, 156, 140, 130, 130, 119, 112, 106,
107, 86, 79, 50, 41, 34, 30, 29, 27, 26, 31, 34, 46, 54, 64, 72, 76, 87, 92,
101, 108, 117, 130, 144, 159, 172, 180, 185, 193, 202, 200, 201, 188, 184, 178,
173, 168, 153, 152, 143, 137, 125, 114, 100, 82, 71, 64, 60, 58, 56, 54, 57, 59,
66, 72, 82, 84, 85, 93, 97, 105, 104, 116, 122, 133, 148, 155, 170, 176, 184,
189, 193, 205, 208, 212, 207, 198, 197, 187, 185, 181, 178, 167, 156, 156, 145,
141, 130, 115, 102, 93, 85, 79, 75, 71, 69, 64, 65, 63, 70, 73, 80, 83, 89, 92,
94, 100, 104, 110, 111, 120, 123, 134, 139, 151, 160, 168, 175, 179, 188, 191,
199, 202, 207, 204, 201, 197, 190, 185, 181, 179, 177, 171, 165, 158, 152, 147,
139, 136, 126, 115, 107, 95, 89, 84, 80, 77, 75, 73, 71, 71, 69, 72, 75, 78, 82,
87, 88, 91, 93, 96, 102, 105, 107, 112, 115, 118, 126, 132, 140, 145, 155, 157,
163, 168, 172, 178, 180, 185, 187, 189, 189, 189, 183, 182, 176, 174, 171, 169,
167, 164, 159, 152, 149, 145, 142, 137, 134, 127, 120, 112, 104, 100, 93, 91,
89, 85, 83, 82, 79, 79, 78, 77, 77, 79, 81, 84, 88, 88, 92, 95, 94, 98, 100,
102, 106, 109, 112, 114, 117, 120, 124, 130, 135, 140, 145, 149, 154, 158, 160,
163, 167, 169, 173, 175, 177, 180, 179, 180, 178, 175, 172, 170, 167, 166, 165,
162, 160, 159, 153, 150, 147, 144, 141, 137, 134, 132, 127, 121, 117, 111, 106,
101, 98, 95, 93, 91, 89, 88, 86, 85, 84, 83, 82, 83, 83, 84, 86, 88, 90, 92, 94,
96, 97, 99, 101, 102, 105, 108, 110, 113, 114, 117, 120, 122, 124, 128, 131,
135, 139, 142, 147, 150, 153, 156, 158, 160, 162, 165, 168, 169, 170, 173, 174,
175, 175, 175, 174, 172, 171, 168, 166, 165, 163, 161, 159, 158, 156, 155, 152,
147, 146, 142, 140, 138, 135, 134, 130, 127, 124, 121, 116, 112, 108, 105, 101,
98, 96, 94, 93, 92, 90, 89, 88, 87, 87, 86, 85, 85, 86, 86, 86, 88, 89, 91, 93,
95, 96, 98, 99, 101, 103, 104, 106, 108, 111, 113, 115, 117, 119, 121, 123, 124,
127, 128, 132, 134, 137, 141, 143, 146, 149, 152, 153, 156, 158, 159, 162, 163,
165, 166, 167, 169, 171, 171, 172, 172, 173, 173, 172, 172, 169, 168, 166, 164,
162, 161, 159, 158, 156, 155, 153, 152, 150, 149, 146, 143, 141, 138, 137, 134,
132, 130, 128, 126, 123, 121, 118, 115, 113, 109, 107, 103, 101, 99, 97, 96, 94,
92, 92, 91, 90, 89, 88, 88, 87, 88, 87, 87, 88, 87, 88, 89, 89, 91, 92, 93, 96,
97, 98, 100, 102, 103, 105, 106, 108, 110, 111, 112, 115, 117, 119, 121, 123,
124, 126, 128, 129, 131, 132, 135, 137, 139, 141, 143, 146, 148, 150, 152, 153,
156, 157, 158, 160, 161, 162, 163, 164, 165, 166, 166, 167, 168, 169, 169, 169,
169, 170, 169, 168, 167, 165, 164, 162, 161, 159, 158, 157, 155, 153, 152, 150,
149, 147, 146, 145, 143, 142, 140, 139, 136, 134, 132, 130, 128, 127, 125, 123,
122, 120, 119, 117, 115, 114, 112, 109, 108, 106, 104, 102, 100, 99, 98, 97, 96,
95, 94, 94, 93, 93, 93, 92, 93, 92, 92, 92, 93, 93, 93, 94, 94, 95, 95, 97, 97,
98, 100, 101, 102, 104, 106, 107, 109, 110, 111, 112, 114, 115, 117, 118, 119,
120, 122, 124, 125, 127, 128, 129, 131, 132, 133, 134, 135, 137, 138, 139, 140,
141, 143, 144, 145, 147, 148, 149, 151, 152, 152, 153, 154, 155, 156, 156, 157,
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
};

#endif /* BD_H_ */
