wgd-modular/utf-8-samplified/firmware/jungle/CH.h

#ifndef CH_H_
#define CH_H_
 
const uint16_t CHLen = 3000; 

const uint8_t  CH[3000] PROGMEM = {128, 128, 128, 128, 129, 129, 129, 129, 129,
129, 129, 129, 129, 130, 130, 130, 130, 130, 130, 130, 130, 130, 130, 130, 130,
131, 130, 130, 130, 130, 130, 129, 129, 130, 130, 130, 129, 128, 128, 129, 130,
130, 130, 130, 129, 128, 128, 130, 132, 134, 134, 132, 131, 132, 133, 136, 137,
137, 137, 137, 137, 137, 137, 137, 137, 138, 138, 139, 138, 139, 139, 139, 138,
138, 136, 138, 137, 140, 135, 128, 144, 146, 134, 124, 121, 151, 159, 132, 108,
116, 179, 150, 103, 176, 175, 150, 74, 1, 86, 169, 209, 163, 174, 159, 151, 90,
8, 57, 140, 223, 191, 200, 140, 97, 152, 82, 8, 66, 131, 198, 182, 223, 123, 31,
105, 102, 167, 188, 129, 93, 210, 199, 95, 63, 75, 64, 100, 136, 101, 132, 190,
115, 44, 51, 3, 136, 246, 211, 196, 218, 186, 155, 189, 39, 43, 79, 108, 134,
45, 140, 126, 162, 131, 65, 149, 234, 182, 184, 144, 100, 237, 181, 102, 69, 95,
113, 77, 76, 38, 76, 122, 74, 60, 71, 162, 108, 187, 173, 108, 158, 144, 207,
181, 152, 131, 145, 148, 205, 135, 136, 169, 159, 192, 155, 174, 178, 190, 179,
119, 147, 125, 164, 199, 109, 50, 56, 115, 97, 85, 72, 86, 22, 123, 80, 99, 181,
162, 166, 133, 141, 122, 205, 197, 137, 87, 188, 109, 174, 115, 31, 99, 94, 161,
139, 40, 60, 159, 152, 155, 33, 171, 182, 110, 204, 131, 116, 203, 104, 158,
121, 86, 107, 116, 219, 75, 70, 129, 100, 152, 150, 43, 95, 107, 149, 110, 70,
123, 103, 103, 135, 42, 99, 156, 67, 149, 104, 135, 128, 136, 147, 106, 188,
128, 142, 214, 155, 160, 192, 133, 134, 160, 125, 98, 102, 117, 110, 95, 138,
97, 76, 147, 109, 204, 164, 122, 170, 160, 78, 81, 142, 95, 163, 106, 64, 160,
170, 158, 145, 147, 165, 106, 185, 136, 100, 142, 71, 84, 156, 76, 49, 171, 141,
153, 122, 120, 188, 198, 190, 127, 155, 213, 175, 174, 108, 67, 105, 157, 105,
34, 110, 49, 90, 147, 94, 78, 114, 120, 108, 149, 102, 139, 168, 175, 103, 59,
188, 151, 168, 146, 35, 175, 172, 169, 144, 111, 152, 167, 121, 99, 135, 148,
207, 48, 127, 134, 108, 149, 106, 139, 80, 66, 138, 151, 93, 105, 88, 147, 104,
99, 104, 145, 135, 115, 93, 65, 129, 137, 134, 63, 96, 100, 133, 110, 129, 88,
81, 155, 124, 156, 134, 50, 168, 163, 134, 135, 92, 130, 88, 161, 106, 90, 111,
172, 105, 116, 69, 50, 224, 136, 100, 68, 119, 176, 142, 132, 90, 117, 176, 91,
119, 131, 128, 173, 156, 82, 56, 129, 164, 144, 126, 120, 60, 128, 126, 100,
163, 119, 98, 110, 112, 119, 102, 179, 70, 71, 128, 44, 113, 132, 155, 138, 101,
64, 136, 122, 183, 143, 92, 171, 48, 154, 124, 88, 184, 112, 107, 120, 107, 135,
174, 157, 151, 160, 123, 156, 136, 158, 139, 110, 145, 110, 131, 113, 80, 98,
147, 111, 125, 137, 145, 170, 155, 122, 155, 171, 151, 125, 115, 154, 131, 163,
97, 83, 82, 78, 108, 145, 157, 151, 105, 87, 167, 151, 138, 140, 157, 153, 99,
75, 130, 147, 150, 79, 72, 56, 132, 150, 93, 156, 96, 144, 138, 107, 140, 149,
136, 156, 61, 111, 132, 129, 142, 53, 108, 89, 111, 138, 134, 95, 136, 105, 136,
130, 103, 143, 129, 137, 92, 118, 141, 147, 131, 94, 66, 145, 166, 123, 94, 110,
123, 134, 143, 110, 110, 174, 133, 112, 128, 94, 162, 148, 153, 106, 90, 110,
116, 162, 137, 67, 111, 138, 126, 119, 83, 95, 168, 98, 71, 117, 59, 179, 145,
104, 81, 106, 154, 137, 85, 103, 155, 157, 165, 93, 106, 107, 168, 159, 129,
120, 145, 169, 143, 93, 118, 123, 151, 174, 61, 93, 130, 158, 137, 92, 101, 152,
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

#endif /* CH_H_ */
