wgd-modular/utf-8-samplified/firmware/808/OH.h

#ifndef OH_H_
#define OH_H_
 
const uint16_t OHLen = 3000; 

const uint8_t  OH[3000] PROGMEM = {145, 103, 139, 124, 169, 112, 61, 201, 107,
115, 209, 2, 179, 164, 92, 125, 132, 154, 80, 217, 15, 190, 131, 99, 125, 205,
34, 173, 114, 138, 139, 79, 195, 62, 192, 66, 182, 90, 134, 167, 95, 85, 213,
66, 178, 82, 167, 140, 64, 212, 59, 173, 136, 89, 208, 2, 247, 88, 67, 230, 18,
239, 36, 201, 61, 174, 128, 110, 136, 104, 149, 170, 73, 127, 152, 118, 145, 89,
167, 98, 139, 152, 93, 123, 179, 71, 168, 113, 104, 176, 113, 101, 164, 94, 149,
125, 144, 82, 163, 116, 168, 86, 110, 189, 78, 143, 141, 89, 176, 121, 76, 192,
94, 169, 44, 234, 20, 211, 96, 119, 161, 81, 175, 61, 242, 1, 216, 96, 109, 168,
96, 130, 157, 114, 105, 157, 111, 130, 133, 132, 95, 188, 74, 179, 73, 147, 156,
73, 181, 100, 141, 155, 69, 142, 165, 70, 194, 60, 210, 35, 208, 83, 132, 145,
85, 217, 15, 226, 51, 197, 80, 141, 102, 190, 96, 130, 103, 150, 148, 67, 210,
45, 194, 93, 128, 151, 120, 106, 149, 118, 134, 131, 119, 127, 155, 85, 142,
147, 120, 122, 147, 109, 130, 112, 155, 122, 111, 153, 116, 115, 142, 139, 107,
156, 85, 155, 142, 110, 108, 185, 60, 171, 101, 190, 53, 162, 132, 114, 131,
124, 155, 90, 169, 77, 189, 72, 173, 79, 171, 109, 128, 144, 108, 130, 137, 115,
142, 120, 131, 129, 136, 100, 133, 172, 68, 163, 135, 119, 113, 133, 123, 150,
130, 97, 150, 138, 81, 164, 144, 110, 116, 129, 161, 80, 147, 142, 120, 163, 64,
160, 108, 161, 119, 105, 151, 123, 114, 163, 66, 190, 128, 77, 162, 118, 130,
100, 205, 60, 152, 111, 174, 86, 126, 133, 146, 116, 127, 129, 125, 134, 134,
116, 116, 152, 119, 157, 48, 211, 95, 124, 127, 159, 83, 153, 125, 122, 152, 65,
212, 83, 129, 129, 118, 149, 148, 67, 164, 148, 81, 172, 100, 121, 143, 157, 86,
153, 92, 164, 124, 108, 154, 89, 189, 71, 162, 101, 153, 109, 155, 91, 155, 117,
128, 178, 24, 211, 109, 115, 120, 164, 95, 141, 138, 108, 139, 137, 90, 208, 27,
181, 160, 43, 222, 49, 191, 74, 181, 79, 150, 138, 107, 166, 67, 162, 131, 131,
124, 138, 102, 135, 118, 178, 62, 149, 166, 101, 115, 125, 160, 95, 176, 48,
201, 103, 107, 160, 118, 121, 123, 128, 169, 86, 121, 162, 88, 182, 61, 194, 67,
175, 103, 127, 140, 127, 134, 111, 143, 105, 140, 151, 73, 187, 118, 65, 225,
47, 174, 115, 120, 126, 147, 117, 130, 124, 131, 131, 130, 104, 161, 117, 117,
147, 108, 131, 142, 135, 95, 155, 111, 146, 115, 136, 118, 133, 138, 101, 167,
101, 122, 159, 85, 175, 86, 157, 113, 130, 140, 107, 142, 131, 132, 103, 140,
133, 136, 111, 161, 91, 139, 117, 150, 118, 112, 170, 87, 144, 123, 118, 174,
73, 149, 140, 116, 128, 120, 154, 89, 155, 122, 139, 117, 129, 118, 144, 116,
136, 125, 121, 148, 104, 157, 82, 179, 95, 153, 116, 106, 167, 97, 137, 139,
116, 117, 170, 80, 143, 143, 121, 105, 172, 82, 157, 119, 120, 159, 82, 168, 95,
162, 89, 166, 104, 134, 135, 108, 148, 125, 119, 153, 102, 130, 132, 127, 145,
82, 193, 66, 174, 111, 125, 134, 120, 136, 120, 144, 105, 149, 117, 126, 137,
122, 127, 135, 117, 141, 115, 133, 131, 124, 132, 126, 122, 133, 134, 101, 168,
106, 133, 138, 84, 187, 83, 155, 112, 140, 121, 122, 150, 85, 181, 95, 126, 153,
96, 150, 126, 111, 163, 81, 165, 130, 99, 145, 117, 144, 119, 130, 137, 110,
135, 126, 129, 138, 118, 134, 134, 118, 113, 160, 108, 120, 154, 108, 137, 122,
129, 130, 129, 121, 138, 120, 132, 129, 124, 143, 105, 132, 145, 122, 115, 142,
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

#endif /* OH_H_ */
