wgd-modular/utf-8-samplified/firmware/808/RD.h

#ifndef RD_H_
#define RD_H_

const uint16_t RDLen = 2058; 
const uint8_t RD[2058] PROGMEM = {127, 130, 119, 85, 82, 80, 78, 76, 74, 73,
74, 75, 93, 116, 132, 142, 138, 164, 146, 168, 176, 158, 188, 187, 187, 190,
191, 200, 178, 187, 204, 154, 187, 176, 166, 166, 151, 133, 138, 142, 140, 116,
91, 122, 100, 112, 88, 87, 93, 101, 63, 91, 88, 60, 103, 81, 86, 87, 75, 93,
102, 69, 94, 109, 96, 104, 109, 108, 128, 110, 121, 118, 134, 146, 150, 161,
127, 153, 186, 160, 153, 193, 160, 168, 197, 174, 166, 191, 162, 170, 180, 159,
155, 152, 155, 157, 137, 124, 130, 119, 130, 114, 114, 103, 106, 95, 106, 103,
69, 89, 101, 92, 82, 89, 97, 89, 89, 98, 98, 94, 91, 105, 110, 116, 105, 112,
121, 115, 122, 138, 131, 152, 133, 132, 162, 139, 172, 155, 157, 165, 154, 173,
168, 168, 176, 151, 162, 169, 165, 157, 145, 158, 139, 147, 145, 146, 119, 114,
130, 122, 119, 108, 121, 96, 94, 108, 101, 99, 97, 102, 96, 84, 98, 95, 99, 109,
82, 107, 109, 107, 118, 106, 102, 123, 131, 120, 114, 130, 147, 124, 146, 145,
135, 147, 161, 144, 159, 161, 147, 162, 153, 164, 165, 160, 151, 152, 154, 148,
159, 154, 127, 147, 138, 144, 125, 128, 130, 108, 131, 103, 126, 110, 96, 111,
108, 105, 102, 102, 100, 103, 99, 110, 96, 107, 103, 93, 125, 108, 101, 124,
115, 117, 115, 132, 131, 120, 134, 136, 136, 145, 145, 129, 151, 149, 154, 153,
142, 162, 145, 150, 160, 148, 155, 147, 149, 151, 140, 148, 138, 139, 138, 142,
127, 118, 130, 127, 122, 119, 115, 115, 120, 100, 109, 109, 105, 112, 113, 98,
97, 114, 107, 111, 105, 116, 109, 106, 117, 117, 119, 121, 126, 126, 119, 123,
142, 129, 144, 132, 132, 147, 143, 145, 145, 147, 147, 153, 141, 145, 150, 153,
139, 149, 148, 145, 144, 139, 140, 136, 137, 133, 128, 132, 131, 117, 122, 128,
119, 110, 117, 113, 119, 110, 108, 116, 110, 110, 107, 112, 110, 110, 115, 111,
112, 114, 121, 118, 119, 126, 122, 123, 128, 124, 131, 138, 129, 141, 133, 138,
142, 137, 150, 142, 141, 141, 144, 150, 142, 141, 150, 141, 141, 141, 138, 139,
136, 137, 138, 132, 128, 128, 123, 136, 117, 123, 124, 114, 121, 119, 118, 108,
118, 112, 119, 110, 111, 117, 107, 115, 117, 116, 117, 117, 119, 119, 123, 126,
116, 125, 130, 129, 131, 131, 134, 135, 137, 130, 140, 140, 136, 145, 140, 138,
138, 144, 144, 139, 143, 141, 133, 144, 140, 129, 141, 138, 125, 133, 132, 133,
127, 124, 126, 118, 126, 123, 122, 115, 120, 121, 111, 118, 116, 121, 112, 115,
118, 117, 121, 110, 119, 122, 121, 122, 121, 127, 126, 118, 131, 127, 129, 133,
130, 139, 128, 133, 138, 138, 133, 137, 141, 139, 139, 138, 139, 139, 141, 136,
133, 135, 140, 133, 134, 135, 132, 132, 132, 127, 125, 130, 125, 128, 123, 116,
127, 121, 118, 121, 121, 117, 123, 113, 115, 123, 116, 121, 117, 119, 120, 120,
121, 124, 123, 128, 121, 125, 129, 127, 127, 133, 131, 128, 134, 135, 136, 130,
138, 133, 135, 142, 136, 133, 138, 139, 138, 135, 134, 140, 131, 133, 137, 128,
135, 129, 128, 131, 131, 125, 123, 127, 124, 125, 121, 124, 126, 117, 122, 122,
117, 123, 118, 120, 122, 121, 117, 120, 122, 124, 123, 120, 128, 123, 124, 128,
126, 131, 128, 126, 133, 132, 128, 135, 135, 131, 135, 132, 136, 135, 136, 138,
130, 135, 136, 136, 136, 131, 133, 134, 131, 136, 128, 129, 133, 126, 128, 129,
127, 126, 126, 122, 124, 124, 125, 123, 121, 119, 122, 123, 120, 124, 121, 119,
124, 123, 121, 124, 125, 125, 123, 124, 127, 125, 128, 128, 130, 131, 126, 130,
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

#endif /* RD.WAV_H_ */
