wgd-modular/utf-8-samplified/firmware/808/SD.h

#ifndef SD_H_
#define SD_H_

const uint16_t SDLen = 2013; 
const uint8_t SD[2013] PROGMEM = {127, 129, 112, 105, 96, 96, 85, 88, 78,
89, 88, 79, 101, 151, 117, 123, 172, 174, 181, 183, 200, 158, 165, 199, 195,
132, 159, 159, 153, 115, 150, 108, 77, 128, 62, 125, 121, 58, 117, 134, 73, 130,
145, 135, 144, 166, 126, 179, 138, 152, 188, 135, 165, 139, 174, 98, 115, 148,
93, 88, 120, 81, 67, 107, 115, 53, 63, 117, 97, 107, 98, 135, 103, 146, 151,
118, 162, 136, 160, 188, 162, 126, 161, 169, 149, 166, 120, 134, 144, 134, 123,
123, 115, 121, 140, 73, 126, 130, 118, 107, 130, 145, 122, 165, 115, 136, 139,
145, 167, 134, 121, 122, 151, 139, 127, 124, 114, 119, 105, 117, 88, 113, 105,
80, 145, 74, 87, 156, 72, 126, 139, 110, 133, 143, 155, 116, 151, 132, 161, 140,
143, 166, 145, 137, 131, 149, 132, 148, 109, 126, 136, 133, 126, 125, 142, 109,
105, 128, 140, 129, 132, 128, 133, 131, 135, 132, 136, 132, 131, 156, 103, 107,
160, 120, 101, 129, 126, 135, 87, 94, 129, 116, 123, 116, 90, 111, 133, 117,
144, 106, 113, 139, 143, 113, 144, 146, 135, 140, 140, 161, 113, 154, 127, 145,
131, 125, 163, 122, 138, 111, 123, 142, 130, 131, 128, 129, 120, 144, 114, 131,
132, 106, 143, 135, 133, 128, 133, 127, 119, 128, 129, 121, 145, 97, 124, 122,
106, 130, 123, 136, 78, 123, 138, 118, 99, 142, 113, 132, 140, 96, 135, 138,
158, 104, 132, 140, 154, 133, 122, 145, 131, 131, 157, 128, 120, 140, 119, 146,
131, 134, 126, 140, 118, 127, 131, 141, 127, 117, 126, 120, 135, 147, 115, 121,
137, 112, 129, 144, 123, 99, 139, 120, 143, 107, 110, 127, 136, 112, 113, 131,
116, 132, 103, 132, 119, 132, 132, 124, 132, 125, 116, 147, 141, 112, 136, 139,
137, 133, 136, 132, 138, 130, 144, 127, 120, 147, 140, 119, 114, 143, 138, 130,
116, 127, 136, 134, 138, 113, 114, 140, 127, 133, 130, 114, 121, 138, 130, 109,
132, 126, 120, 117, 133, 127, 112, 136, 116, 112, 141, 121, 110, 132, 143, 110,
114, 134, 145, 125, 113, 140, 121, 140, 131, 136, 131, 131, 138, 125, 133, 133,
146, 123, 125, 129, 133, 139, 128, 137, 130, 114, 145, 125, 116, 138, 125, 140,
120, 113, 137, 126, 135, 127, 113, 135, 114, 130, 138, 112, 127, 129, 112, 133,
125, 117, 141, 109, 126, 128, 127, 128, 126, 118, 134, 136, 110, 136, 127, 125,
133, 131, 135, 134, 120, 143, 123, 129, 136, 135, 139, 117, 133, 136, 131, 133,
133, 124, 126, 142, 127, 118, 137, 123, 142, 114, 125, 134, 129, 133, 114, 134,
126, 121, 129, 132, 112, 131, 127, 118, 128, 128, 131, 115, 120, 134, 124, 131,
126, 117, 126, 137, 126, 122, 131, 123, 130, 128, 137, 124, 124, 143, 125, 124,
136, 131, 135, 128, 133, 130, 128, 136, 124, 128, 137, 132, 125, 129, 132, 137,
116, 132, 127, 132, 129, 118, 135, 123, 131, 124, 130, 131, 115, 125, 130, 126,
125, 129, 124, 118, 131, 125, 134, 120, 116, 134, 123, 128, 128, 127, 126, 134,
128, 122, 121, 133, 132, 131, 129, 130, 134, 124, 134, 126, 130, 128, 133, 133,
130, 131, 130, 130, 131, 130, 134, 123, 121, 135, 135, 129, 119, 136, 131, 123,
125, 126, 130, 127, 127, 132, 122, 122, 128, 126, 121, 133, 129, 115, 136, 122,
122, 130, 129, 122, 128, 128, 128, 129, 120, 131, 129, 129, 129, 134, 120, 133,
127, 123, 138, 129, 122, 137, 131, 124, 136, 124, 135, 127, 130, 132, 132, 130,
122, 132, 135, 122, 127, 135, 121, 132, 127, 126, 133, 125, 122, 126, 134, 121,
129, 131, 121, 126, 124, 127, 126, 129, 126, 127, 126, 126, 127, 127, 131, 120,
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

#endif /* SD.WAV_H_ */
