wgd-modular/utf-8-samplified/firmware/beatbox/BD.h

#ifndef BD_H_
#define BD_H_
 
const uint16_t BDLen = 2249; 
const uint8_t  BD[2249] PROGMEM = {128, 128, 128, 128, 128, 125, 123, 126, 129,
129, 132, 138, 131, 125, 119, 111, 122, 120, 105, 96, 101, 108, 118, 110, 109,
112, 111, 123, 117, 108, 112, 117, 95, 80, 112, 119, 115, 127, 111, 165, 151,
89, 131, 171, 104, 109, 130, 123, 140, 134, 178, 135, 135, 190, 118, 140, 178,
136, 164, 147, 143, 143, 191, 123, 147, 191, 153, 167, 142, 206, 154, 154, 165,
137, 150, 139, 147, 153, 131, 150, 153, 134, 106, 205, 144, 109, 175, 91, 159,
119, 123, 160, 115, 77, 158, 135, 108, 173, 116, 107, 159, 101, 148, 111, 117,
154, 54, 137, 113, 168, 47, 122, 141, 91, 158, 82, 123, 135, 87, 72, 107, 103,
99, 81, 133, 116, 86, 148, 155, 48, 164, 104, 97, 108, 58, 172, 90, 127, 98,
161, 118, 104, 138, 66, 199, 77, 109, 178, 96, 184, 108, 122, 142, 130, 165, 93,
194, 95, 112, 221, 91, 196, 151, 102, 147, 203, 178, 34, 255, 137, 64, 238, 103,
144, 131, 206, 101, 119, 225, 88, 185, 152, 110, 139, 138, 153, 128, 179, 121,
117, 181, 136, 187, 112, 144, 92, 170, 155, 106, 131, 142, 152, 68, 222, 108,
125, 161, 148, 116, 186, 159, 101, 152, 142, 121, 76, 167, 144, 132, 142, 149,
170, 146, 122, 182, 101, 163, 144, 113, 187, 107, 123, 155, 124, 144, 162, 136,
111, 122, 209, 94, 166, 160, 103, 195, 142, 140, 150, 146, 166, 120, 170, 146,
138, 157, 107, 174, 109, 187, 105, 130, 203, 82, 146, 154, 119, 161, 123, 139,
104, 156, 151, 128, 148, 64, 180, 107, 138, 152, 80, 164, 125, 76, 145, 143,
136, 79, 156, 118, 138, 181, 88, 113, 176, 118, 122, 138, 87, 164, 88, 156, 91,
171, 111, 134, 159, 104, 198, 96, 154, 140, 121, 155, 136, 142, 118, 139, 132,
103, 162, 129, 130, 155, 148, 146, 171, 124, 144, 128, 173, 98, 148, 172, 125,
143, 131, 194, 93, 183, 183, 138, 183, 164, 122, 192, 119, 166, 163, 159, 136,
132, 193, 146, 215, 145, 177, 151, 183, 204, 165, 167, 200, 142, 161, 198, 173,
185, 156, 163, 146, 177, 164, 177, 195, 157, 174, 196, 177, 177, 171, 188, 180,
151, 182, 177, 169, 177, 151, 191, 150, 166, 184, 192, 185, 158, 172, 161, 203,
140, 178, 168, 149, 181, 164, 188, 171, 176, 181, 158, 178, 160, 162, 172, 149,
178, 135, 157, 153, 139, 194, 127, 155, 160, 139, 163, 128, 157, 136, 139, 148,
129, 157, 117, 129, 136, 112, 149, 122, 128, 111, 108, 114, 93, 99, 93, 111,
102, 110, 112, 100, 99, 97, 87, 99, 94, 75, 87, 88, 76, 70, 72, 75, 74, 77, 58,
72, 82, 70, 73, 70, 75, 65, 63, 78, 64, 61, 71, 60, 80, 66, 67, 80, 79, 88, 75,
89, 97, 86, 99, 99, 103, 94, 105, 118, 103, 112, 111, 117, 126, 137, 125, 135,
133, 131, 143, 149, 149, 140, 142, 150, 157, 156, 163, 171, 179, 171, 182, 177,
182, 182, 171, 193, 177, 179, 195, 178, 201, 185, 190, 189, 181, 206, 189, 203,
197, 198, 198, 202, 211, 201, 206, 193, 193, 199, 201, 208, 195, 195, 187, 192,
191, 199, 195, 196, 192, 187, 186, 177, 194, 178, 190, 181, 185, 182, 180, 176,
168, 169, 168, 168, 170, 172, 158, 166, 149, 151, 149, 142, 144, 135, 130, 126,
118, 120, 115, 122, 105, 119, 111, 103, 114, 93, 107, 87, 96, 95, 82, 93, 83,
85, 87, 79, 93, 87, 82, 84, 86, 83, 80, 76, 77, 70, 58, 62, 57, 66, 53, 59, 52,
57, 64, 58, 61, 50, 51, 51, 53, 48, 50, 47, 43, 45, 46, 36, 45, 41, 44, 48, 48,
54, 40, 55, 48, 46, 49, 38, 47, 47, 51, 62, 58, 62, 52, 76, 69, 69, 79, 66, 81,
72, 81, 90, 90, 94, 100, 98, 116, 121, 124, 130, 136, 132, 132, 134, 136, 140,
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

#endif /* BD_H_ */
