wgd-modular/utf-8-samplified/firmware/beatbox/CL.h

#ifndef CL_H_
#define CL_H_
 
const uint16_t CLLen = 2331; 
const uint8_t  CL[2331] PROGMEM = {128, 128, 126, 127, 129, 128, 130, 129, 127,
126, 125, 128, 131, 129, 126, 130, 124, 127, 128, 127, 126, 127, 134, 129, 116,
127, 124, 120, 135, 123, 131, 128, 119, 127, 118, 128, 125, 127, 128, 120, 138,
117, 128, 126, 124, 130, 122, 139, 121, 134, 124, 116, 133, 122, 131, 122, 131,
130, 125, 137, 114, 125, 132, 113, 121, 145, 128, 124, 129, 126, 132, 109, 138,
121, 117, 136, 90, 157, 117, 133, 155, 74, 166, 93, 120, 146, 84, 171, 122, 97,
148, 120, 133, 122, 80, 161, 125, 120, 139, 103, 182, 78, 137, 132, 115, 173,
12, 210, 120, 85, 166, 68, 189, 118, 110, 161, 86, 120, 145, 87, 165, 120, 159,
126, 80, 159, 91, 157, 108, 155, 125, 98, 139, 86, 203, 100, 115, 145, 106, 146,
123, 149, 104, 92, 158, 122, 126, 131, 110, 138, 126, 143, 100, 150, 156, 100,
97, 155, 127, 156, 116, 64, 171, 118, 157, 140, 95, 166, 108, 129, 121, 120,
130, 107, 175, 67, 118, 42, 153, 140, 80, 178, 111, 107, 52, 158, 157, 166, 84,
137, 161, 59, 131, 146, 118, 157, 97, 166, 100, 125, 179, 42, 186, 103, 178, 57,
117, 246, 31, 144, 176, 83, 138, 127, 130, 118, 128, 173, 95, 154, 91, 163, 133,
118, 166, 80, 132, 169, 131, 116, 169, 91, 143, 147, 66, 215, 137, 109, 122,
129, 162, 94, 161, 132, 154, 68, 137, 149, 157, 163, 60, 124, 155, 179, 62, 171,
151, 83, 124, 143, 208, 70, 75, 214, 111, 121, 134, 87, 180, 94, 150, 98, 160,
179, 55, 130, 165, 61, 137, 222, 34, 154, 119, 127, 155, 116, 94, 127, 177, 97,
137, 103, 175, 69, 126, 200, 75, 143, 110, 151, 96, 122, 207, 60, 141, 125, 153,
109, 89, 203, 73, 233, 51, 108, 120, 122, 226, 38, 185, 148, 80, 133, 165, 119,
119, 92, 152, 137, 134, 138, 150, 106, 142, 127, 74, 188, 103, 106, 156, 142,
152, 130, 84, 143, 171, 115, 64, 190, 140, 113, 117, 136, 153, 162, 119, 96,
151, 70, 187, 118, 154, 103, 100, 187, 109, 124, 120, 161, 99, 114, 162, 90,
143, 153, 123, 156, 117, 119, 119, 149, 89, 180, 106, 135, 153, 96, 158, 97,
143, 115, 151, 101, 177, 92, 136, 130, 97, 114, 156, 164, 126, 170, 93, 123, 86,
160, 105, 155, 127, 138, 162, 105, 107, 138, 134, 162, 92, 141, 171, 82, 133,
97, 158, 70, 213, 103, 153, 143, 111, 159, 64, 188, 27, 164, 175, 81, 180, 131,
128, 131, 105, 135, 106, 175, 56, 122, 206, 62, 215, 50, 197, 116, 37, 238, 33,
222, 78, 139, 150, 111, 200, 26, 183, 82, 124, 172, 135, 116, 124, 141, 112,
139, 133, 95, 125, 142, 110, 153, 109, 141, 119, 129, 127, 141, 158, 1, 227,
122, 39, 210, 110, 163, 96, 175, 97, 118, 77, 179, 110, 119, 204, 69, 202, 54,
125, 124, 179, 96, 118, 161, 111, 134, 133, 151, 87, 149, 117, 148, 105, 148,
153, 102, 178, 81, 161, 116, 105, 143, 120, 128, 124, 177, 124, 141, 99, 120,
108, 198, 70, 172, 121, 101, 195, 90, 177, 69, 130, 138, 111, 178, 150, 95, 164,
92, 157, 114, 102, 153, 156, 140, 127, 126, 114, 125, 134, 129, 154, 126, 150,
130, 78, 162, 79, 201, 88, 147, 167, 141, 74, 133, 145, 122, 132, 118, 150, 104,
206, 64, 140, 152, 110, 103, 191, 86, 145, 126, 146, 151, 88, 165, 118, 168, 78,
183, 106, 160, 137, 125, 146, 119, 127, 112, 183, 116, 157, 90, 141, 193, 52,
189, 126, 128, 148, 110, 173, 81, 164, 97, 146, 150, 148, 137, 128, 81, 192,
110, 109, 186, 71, 167, 87, 157, 146, 128, 114, 163, 118, 138, 126, 163, 82,
118, 152, 98, 181, 131, 131, 129, 162, 85, 150, 99, 171, 101, 140, 153, 95, 187,
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

#endif /* CL_H_ */
