wgd-modular/utf-8-samplified/firmware/beatbox/CR.h

#ifndef CR_H_
#define CR_H_
 
const uint16_t CRLen = 2605; 
const uint8_t  CR[2605] PROGMEM = {129, 130, 129, 129, 128, 128, 127, 127, 126,
126, 126, 126, 127, 127, 128, 128, 129, 130, 130, 130, 130, 130, 130, 130, 129,
128, 128, 127, 127, 126, 126, 126, 126, 126, 127, 128, 128, 129, 130, 130, 130,
130, 130, 130, 129, 129, 128, 127, 127, 126, 126, 126, 126, 127, 127, 128, 129,
129, 130, 130, 131, 131, 130, 130, 129, 129, 128, 127, 126, 125, 124, 124, 124,
125, 126, 127, 128, 129, 130, 131, 131, 131, 131, 130, 130, 128, 127, 126, 125,
124, 123, 123, 123, 123, 124, 126, 127, 128, 130, 131, 132, 133, 133, 132, 131,
130, 129, 127, 126, 124, 123, 122, 122, 122, 123, 125, 126, 128, 130, 132, 133,
134, 135, 134, 133, 132, 130, 128, 127, 125, 123, 122, 121, 122, 123, 125, 127,
129, 131, 133, 135, 136, 136, 135, 134, 132, 130, 127, 125, 123, 121, 120, 120,
121, 122, 124, 127, 130, 132, 135, 136, 137, 137, 136, 134, 131, 128, 125, 122,
120, 118, 117, 118, 119, 122, 125, 129, 132, 135, 138, 139, 140, 139, 137, 134,
130, 126, 122, 118, 116, 114, 114, 116, 119, 123, 127, 131, 135, 139, 142, 143,
143, 141, 138, 133, 128, 123, 118, 114, 111, 111, 112, 115, 119, 125, 131, 136,
141, 145, 147, 147, 145, 141, 136, 130, 123, 117, 112, 108, 106, 107, 111, 117,
124, 132, 139, 145, 149, 151, 151, 148, 143, 136, 129, 121, 113, 108, 104, 103,
105, 110, 117, 125, 134, 142, 148, 153, 155, 154, 151, 144, 135, 126, 116, 107,
101, 99, 99, 103, 109, 118, 127, 138, 147, 155, 159, 161, 159, 153, 145, 134,
122, 111, 101, 94, 92, 93, 99, 109, 120, 132, 144, 154, 161, 164, 164, 160, 152,
142, 129, 116, 103, 93, 87, 86, 91, 99, 111, 125, 139, 152, 162, 168, 170, 167,
160, 149, 135, 120, 105, 93, 85, 82, 85, 93, 104, 119, 134, 149, 161, 169, 173,
172, 166, 156, 142, 125, 108, 94, 83, 78, 78, 85, 97, 112, 129, 145, 160, 172,
178, 179, 174, 163, 147, 130, 112, 95, 82, 74, 73, 78, 89, 105, 124, 144, 162,
177, 186, 188, 184, 173, 156, 135, 113, 93, 77, 68, 66, 71, 84, 101, 123, 145,
165, 181, 192, 195, 190, 177, 158, 135, 111, 88, 71, 61, 60, 67, 80, 99, 121,
144, 165, 182, 194, 197, 192, 178, 159, 135, 110, 88, 70, 60, 56, 62, 77, 96,
120, 144, 167, 186, 198, 203, 197, 182, 161, 135, 109, 86, 67, 56, 54, 61, 76,
97, 121, 147, 170, 190, 202, 206, 201, 186, 162, 133, 105, 81, 62, 52, 51, 60,
77, 100, 126, 153, 176, 194, 203, 205, 196, 179, 155, 126, 98, 73, 56, 48, 50,
62, 80, 106, 133, 159, 182, 200, 209, 207, 195, 173, 145, 114, 86, 65, 54, 50,
55, 69, 89, 115, 141, 167, 189, 204, 210, 204, 188, 164, 135, 104, 76, 57, 48,
48, 59, 78, 103, 131, 159, 184, 201, 209, 207, 195, 174, 146, 116, 85, 62, 49,
46, 53, 70, 96, 125, 154, 179, 199, 209, 209, 198, 178, 152, 121, 90, 65, 49,
44, 51, 67, 91, 119, 148, 174, 195, 207, 209, 199, 181, 155, 125, 96, 70, 53,
47, 51, 64, 86, 113, 143, 171, 194, 209, 212, 205, 187, 160, 126, 94, 68, 51,
44, 48, 62, 85, 113, 144, 173, 196, 211, 214, 207, 188, 159, 126, 95, 68, 49,
41, 44, 59, 83, 113, 145, 176, 200, 215, 218, 209, 187, 157, 123, 89, 62, 44,
38, 44, 62, 89, 120, 153, 183, 206, 218, 219, 206, 183, 152, 117, 84, 57, 40,
36, 45, 65, 92, 125, 159, 188, 210, 220, 218, 204, 179, 146, 109, 75, 47, 32,
31, 43, 67, 100, 137, 172, 202, 221, 227, 217, 197, 167, 130, 93, 59, 34, 25,
31, 50, 80, 116, 154, 188, 214, 229, 230, 216, 188, 151, 110, 72, 41, 23, 22,
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

#endif /* CR_H_ */
