wgd-modular/utf-8-samplified/firmware/beatbox/RS.h

#ifndef RS_H_
#define RS_H_
 
const uint16_t RSLen = 2689; 
const uint8_t  RS[2689] PROGMEM = {128, 128, 128, 128, 128, 128, 128, 128, 128,
128, 128, 128, 128, 128, 128, 128, 128, 128, 128, 128, 128, 128, 128, 128, 128,
128, 128, 128, 128, 128, 128, 128, 128, 128, 128, 128, 128, 128, 128, 128, 128,
128, 128, 128, 128, 128, 128, 128, 128, 128, 128, 128, 128, 128, 128, 128, 128,
128, 128, 128, 128, 128, 128, 128, 128, 128, 128, 128, 128, 128, 128, 128, 128,
128, 128, 128, 128, 128, 131, 134, 130, 128, 125, 125, 128, 131, 128, 126, 125,
131, 131, 123, 126, 127, 127, 126, 123, 130, 138, 134, 127, 127, 131, 134, 126,
123, 123, 126, 129, 126, 126, 127, 131, 124, 123, 130, 143, 114, 109, 142, 143,
140, 125, 109, 113, 117, 105, 139, 173, 125, 150, 186, 162, 150, 109, 96, 102,
103, 84, 129, 126, 78, 100, 114, 123, 73, 76, 129, 154, 203, 234, 255, 222, 148,
89, 98, 130, 89, 125, 119, 79, 120, 136, 107, 56, 43, 91, 111, 88, 121, 155,
166, 127, 157, 228, 186, 161, 184, 201, 179, 115, 90, 92, 76, 84, 102, 117, 94,
92, 77, 73, 91, 89, 166, 187, 141, 160, 165, 189, 142, 86, 106, 169, 219, 166,
184, 131, 124, 152, 82, 66, 43, 51, 59, 80, 109, 116, 174, 163, 183, 211, 191,
177, 124, 115, 121, 140, 125, 113, 75, 55, 75, 68, 75, 78, 130, 183, 207, 217,
230, 209, 149, 162, 127, 105, 82, 33, 82, 73, 71, 83, 100, 120, 140, 177, 165,
156, 146, 162, 197, 165, 155, 163, 165, 152, 96, 107, 84, 70, 77, 54, 60, 75,
121, 119, 146, 156, 135, 180, 166, 151, 159, 154, 163, 162, 148, 139, 131, 109,
95, 104, 102, 96, 94, 98, 127, 131, 147, 148, 127, 125, 137, 153, 124, 110, 136,
152, 133, 126, 130, 77, 111, 152, 142, 137, 138, 149, 155, 171, 137, 127, 83,
58, 94, 113, 102, 105, 119, 135, 139, 127, 166, 164, 157, 157, 170, 166, 131,
148, 130, 110, 99, 105, 98, 68, 96, 98, 114, 128, 110, 123, 150, 150, 151, 138,
133, 151, 149, 144, 135, 125, 124, 135, 125, 120, 129, 142, 134, 131, 127, 120,
128, 113, 129, 129, 113, 120, 118, 115, 121, 130, 124, 128, 127, 132, 134, 131,
140, 129, 133, 139, 123, 128, 141, 131, 130, 137, 130, 120, 124, 129, 125, 124,
111, 120, 128, 115, 129, 130, 111, 116, 119, 129, 125, 138, 157, 143, 153, 144,
156, 148, 139, 150, 127, 124, 116, 118, 75, 63, 79, 80, 108, 112, 132, 141, 140,
152, 182, 171, 166, 199, 199, 184, 150, 122, 102, 73, 81, 93, 54, 32, 80, 111,
80, 100, 135, 146, 148, 171, 199, 167, 162, 182, 185, 149, 124, 137, 129, 115,
104, 123, 99, 104, 128, 106, 127, 117, 119, 136, 121, 113, 134, 127, 106, 123,
118, 111, 129, 121, 133, 126, 122, 155, 134, 132, 145, 151, 130, 131, 145, 141,
145, 138, 148, 119, 114, 133, 125, 109, 89, 104, 109, 107, 100, 117, 135, 149,
164, 164, 172, 156, 176, 167, 140, 119, 106, 87, 57, 65, 66, 75, 61, 88, 126,
136, 169, 188, 194, 182, 189, 188, 158, 151, 144, 129, 110, 114, 114, 105, 104,
106, 117, 101, 112, 121, 108, 111, 129, 127, 112, 126, 117, 126, 138, 131, 155,
140, 128, 149, 128, 129, 141, 141, 135, 116, 132, 136, 122, 127, 138, 129, 111,
131, 125, 124, 127, 127, 135, 112, 137, 128, 120, 127, 125, 137, 119, 133, 127,
127, 120, 123, 131, 117, 131, 132, 129, 124, 134, 135, 130, 129, 127, 146, 132,
124, 129, 127, 126, 124, 121, 122, 123, 124, 139, 129, 119, 131, 128, 127, 138,
137, 133, 131, 127, 124, 123, 126, 128, 123, 123, 146, 129, 120, 130, 125, 127,
110, 122, 130, 118, 126, 142, 129, 116, 135, 139, 142, 132, 138, 146, 125, 123,
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

#endif /* RS_H_ */
