wgd-modular/utf-8-samplified/firmware/beatbox/SD.h

#ifndef SD_H_
#define SD_H_
 
const uint16_t SDLen = 5228; 
const uint8_t  SD[5228] PROGMEM = {128, 128, 128, 128, 128, 128, 128, 128, 128,
128, 128, 128, 128, 128, 128, 128, 128, 128, 128, 128, 128, 128, 128, 128, 128,
128, 128, 128, 128, 128, 128, 128, 128, 128, 128, 128, 128, 128, 128, 128, 128,
128, 128, 128, 128, 128, 128, 128, 128, 128, 128, 128, 128, 128, 128, 128, 128,
128, 128, 128, 128, 128, 128, 128, 128, 128, 128, 128, 128, 128, 128, 128, 128,
128, 128, 128, 128, 128, 128, 128, 128, 128, 128, 128, 128, 128, 128, 128, 128,
128, 128, 128, 128, 128, 128, 128, 128, 128, 128, 128, 128, 128, 128, 128, 128,
128, 128, 128, 128, 128, 128, 128, 128, 128, 128, 128, 128, 128, 128, 128, 128,
128, 128, 128, 128, 128, 128, 128, 128, 128, 128, 128, 128, 128, 128, 128, 128,
128, 128, 128, 128, 128, 128, 128, 128, 128, 128, 128, 128, 128, 128, 128, 128,
128, 128, 128, 128, 128, 128, 128, 128, 128, 128, 128, 128, 128, 128, 128, 128,
128, 128, 128, 128, 128, 128, 128, 128, 128, 128, 128, 128, 128, 128, 128, 128,
128, 128, 128, 128, 128, 128, 128, 128, 128, 128, 128, 128, 128, 128, 128, 128,
128, 128, 128, 128, 128, 128, 128, 128, 128, 128, 128, 128, 128, 128, 128, 128,
128, 128, 128, 128, 128, 127, 134, 159, 130, 121, 129, 133, 133, 111, 106, 96,
89, 91, 123, 142, 158, 148, 123, 90, 104, 120, 132, 128, 107, 104, 114, 151,
133, 149, 134, 124, 120, 126, 143, 130, 123, 137, 125, 100, 100, 109, 122, 126,
129, 133, 179, 177, 95, 50, 117, 171, 212, 160, 155, 134, 95, 123, 157, 215,
133, 131, 136, 149, 138, 57, 74, 73, 144, 166, 241, 247, 117, 94, 74, 159, 81,
51, 114, 145, 162, 135, 174, 132, 163, 196, 163, 145, 124, 107, 47, 67, 126,
108, 154, 143, 142, 139, 149, 117, 83, 100, 69, 105, 108, 142, 87, 82, 106, 142,
181, 122, 124, 85, 65, 79, 110, 118, 103, 128, 143, 124, 105, 60, 34, 58, 131,
187, 158, 143, 132, 90, 110, 177, 187, 146, 81, 31, 106, 180, 175, 176, 180,
205, 153, 157, 201, 155, 180, 168, 66, 15, 48, 122, 170, 144, 143, 204, 195,
200, 149, 144, 151, 145, 134, 183, 150, 90, 75, 41, 160, 201, 203, 138, 137,
137, 136, 187, 210, 176, 52, 55, 106, 109, 109, 123, 126, 134, 212, 186, 153,
99, 57, 54, 108, 147, 168, 166, 141, 123, 79, 164, 109, 86, 107, 69, 106, 128,
96, 84, 60, 134, 173, 151, 163, 110, 51, 1, 74, 66, 86, 129, 136, 208, 166, 155,
114, 105, 121, 85, 87, 137, 127, 141, 198, 146, 154, 122, 68, 79, 110, 138, 178,
179, 137, 123, 125, 141, 152, 125, 151, 139, 85, 87, 82, 165, 186, 187, 152, 99,
89, 44, 144, 159, 140, 76, 80, 132, 185, 215, 127, 111, 77, 129, 109, 154, 174,
133, 136, 161, 184, 128, 96, 42, 90, 105, 126, 134, 120, 97, 104, 169, 126, 135,
153, 156, 117, 96, 137, 119, 147, 164, 194, 205, 146, 111, 10, 31, 99, 153, 190,
124, 89, 87, 139, 131, 156, 144, 110, 83, 116, 115, 99, 140, 164, 224, 169, 163,
132, 147, 156, 134, 118, 92, 109, 158, 223, 240, 155, 89, 132, 187, 206, 191,
178, 93, 94, 126, 141, 120, 147, 120, 119, 169, 185, 172, 70, 74, 96, 108, 168,
175, 156, 135, 139, 138, 132, 149, 101, 101, 84, 112, 109, 115, 108, 95, 87,
110, 170, 106, 124, 96, 69, 62, 67, 120, 99, 102, 87, 95, 98, 100, 145, 120,
149, 139, 114, 99, 93, 79, 54, 88, 63, 63, 53, 85, 108, 116, 151, 117, 98, 121,
151, 133, 78, 71, 114, 130, 95, 135, 210, 183, 126, 126, 153, 111, 86, 107, 185,
147, 132, 123, 135, 163, 159, 179, 143, 174, 154, 153, 141, 165, 198, 183, 154,
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

#endif /* SD_H_ */
