wgd-modular/utf-8-samplified/firmware/jungle/CL.h

#ifndef CL_H_
#define CL_H_
 
const uint16_t CLLen = 3000; 
const uint8_t  CL[3000] PROGMEM = {126, 130, 126, 130, 125, 131, 124, 132, 124,
132, 124, 132, 124, 131, 127, 125, 156, 89, 183, 118, 139, 216, 68, 104, 149,
109, 66, 101, 252, 122, 69, 166, 33, 205, 112, 1, 209, 138, 83, 111, 147, 77,
157, 168, 114, 130, 89, 163, 78, 170, 134, 104, 107, 99, 173, 99, 161, 44, 196,
148, 18, 187, 85, 176, 129, 54, 166, 95, 175, 96, 85, 72, 147, 217, 63, 126, 38,
177, 190, 24, 158, 182, 98, 82, 74, 226, 67, 128, 198, 55, 172, 32, 156, 183,
153, 79, 103, 198, 42, 177, 88, 160, 145, 54, 178, 149, 141, 81, 162, 90, 99,
158, 131, 122, 90, 131, 150, 155, 163, 71, 116, 139, 125, 160, 81, 126, 123,
159, 133, 107, 125, 126, 150, 109, 90, 129, 158, 151, 102, 107, 106, 122, 131,
128, 149, 117, 137, 77, 185, 82, 120, 149, 74, 166, 115, 158, 77, 139, 106, 119,
162, 130, 94, 139, 150, 57, 138, 174, 136, 86, 141, 134, 109, 116, 123, 126,
126, 163, 137, 100, 93, 128, 171, 121, 103, 96, 164, 131, 132, 144, 81, 118,
146, 160, 102, 119, 138, 86, 139, 162, 128, 114, 112, 133, 114, 151, 96, 164,
132, 116, 119, 82, 154, 157, 127, 100, 140, 115, 125, 124, 139, 130, 123, 102,
154, 126, 90, 168, 153, 98, 114, 130, 123, 136, 129, 120, 152, 108, 109, 169,
105, 129, 152, 116, 116, 149, 113, 123, 162, 144, 88, 119, 139, 143, 127, 129,
115, 109, 171, 97, 118, 143, 137, 149, 123, 90, 120, 154, 151, 111, 118, 163,
70, 151, 153, 106, 128, 100, 163, 122, 149, 125, 94, 117, 169, 123, 123, 139,
100, 148, 108, 169, 92, 153, 117, 107, 185, 84, 145, 123, 142, 97, 133, 156, 80,
124, 156, 148, 103, 129, 118, 132, 136, 122, 119, 109, 163, 121, 117, 164, 101,
98, 158, 104, 154, 141, 123, 121, 116, 143, 92, 154, 103, 146, 149, 99, 129,
149, 105, 126, 161, 98, 126, 122, 158, 118, 129, 144, 92, 133, 152, 145, 106,
98, 151, 169, 105, 113, 143, 139, 124, 95, 172, 129, 130, 134, 83, 132, 164,
142, 98, 125, 148, 141, 89, 123, 142, 162, 126, 96, 149, 138, 126, 120, 150,
138, 128, 95, 144, 145, 107, 144, 125, 142, 118, 128, 126, 138, 115, 101, 159,
128, 154, 126, 97, 111, 156, 140, 105, 136, 124, 139, 107, 136, 115, 116, 162,
111, 143, 123, 136, 132, 97, 139, 137, 146, 125, 123, 108, 138, 137, 138, 142,
102, 121, 136, 140, 121, 132, 139, 130, 121, 139, 118, 110, 132, 167, 111, 113,
145, 134, 104, 130, 153, 124, 123, 107, 161, 106, 140, 113, 131, 146, 100, 136,
124, 137, 134, 115, 125, 139, 142, 106, 121, 155, 112, 147, 118, 114, 133, 143,
140, 119, 101, 136, 151, 132, 125, 111, 113, 127, 155, 142, 120, 99, 147, 141,
111, 120, 136, 137, 137, 129, 123, 122, 123, 132, 139, 120, 135, 137, 115, 125,
143, 125, 129, 146, 107, 127, 127, 140, 126, 125, 137, 133, 122, 141, 120, 114,
149, 127, 121, 139, 132, 104, 151, 130, 116, 131, 130, 130, 136, 115, 126, 146,
125, 123, 117, 135, 126, 133, 138, 134, 128, 113, 130, 130, 128, 128, 138, 129,
116, 137, 125, 132, 129, 125, 130, 130, 127, 125, 130, 131, 132, 125, 126, 122,
139, 128, 120, 131, 134, 123, 136, 124, 116, 146, 114, 142, 132, 111, 134, 134,
130, 125, 128, 111, 137, 144, 136, 127, 111, 134, 127, 121, 137, 126, 133, 135,
118, 132, 127, 123, 133, 135, 115, 126, 142, 123, 128, 128, 134, 126, 132, 123,
125, 133, 128, 132, 121, 133, 131, 127, 122, 133, 123, 132, 136, 128, 131, 121,
125, 132, 129, 133, 134, 121, 127, 127, 125, 127, 138, 132, 130, 121, 126, 133,
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

#endif /* CL_H_ */
