wgd-modular/utf-8-samplified/firmware/jungle/CR.h

#ifndef CR_H_
#define CR_H_
 
const uint16_t CRLen = 3000; 
const uint8_t  CR[3000] PROGMEM = {128, 128, 128, 128, 128, 128, 127, 129, 126,
130, 127, 133, 127, 133, 121, 129, 131, 123, 131, 123, 137, 117, 139, 120, 130,
127, 122, 136, 117, 134, 123, 130, 127, 130, 125, 131, 126, 128, 130, 129, 127,
127, 131, 123, 134, 119, 132, 124, 127, 129, 125, 130, 124, 132, 124, 132, 125,
131, 127, 126, 127, 128, 129, 125, 129, 124, 132, 122, 132, 124, 128, 124, 127,
131, 125, 126, 131, 129, 122, 134, 121, 137, 118, 134, 126, 131, 122, 133, 122,
130, 126, 130, 122, 129, 134, 115, 138, 127, 121, 111, 169, 68, 186, 82, 151,
128, 98, 174, 81, 175, 73, 173, 102, 131, 139, 114, 144, 98, 142, 156, 75, 158,
131, 111, 145, 117, 140, 101, 168, 90, 153, 122, 121, 147, 105, 151, 114, 137,
111, 151, 109, 137, 151, 1, 201, 126, 106, 148, 117, 142, 115, 144, 112, 172,
24, 135, 178, 86, 149, 127, 119, 136, 124, 123, 139, 115, 137, 128, 121, 147,
110, 143, 121, 130, 133, 117, 144, 109, 147, 102, 152, 105, 142, 126, 119, 146,
107, 145, 114, 147, 105, 146, 121, 127, 129, 130, 122, 133, 127, 122, 142, 107,
144, 123, 124, 134, 126, 123, 138, 117, 139, 120, 130, 128, 131, 124, 127, 132,
121, 134, 124, 131, 126, 125, 133, 125, 127, 125, 126, 137, 115, 141, 117, 137,
119, 136, 123, 130, 122, 135, 123, 135, 121, 129, 133, 118, 141, 112, 140, 120,
138, 117, 141, 118, 139, 117, 138, 121, 133, 128, 121, 141, 117, 130, 133, 121,
131, 129, 125, 133, 118, 142, 116, 135, 126, 132, 124, 134, 128, 129, 123, 137,
115, 138, 126, 125, 130, 129, 128, 122, 134, 123, 133, 117, 142, 115, 138, 124,
130, 128, 129, 129, 126, 131, 123, 133, 123, 134, 124, 130, 132, 122, 135, 120,
137, 122, 133, 128, 126, 133, 122, 142, 116, 137, 122, 128, 131, 125, 133, 124,
128, 133, 121, 133, 127, 125, 134, 121, 137, 120, 136, 123, 128, 130, 125, 133,
123, 134, 122, 133, 124, 133, 127, 125, 133, 124, 131, 127, 131, 124, 134, 122,
131, 131, 122, 139, 120, 130, 135, 117, 142, 118, 134, 133, 119, 140, 120, 136,
123, 134, 123, 133, 123, 132, 132, 120, 134, 128, 128, 130, 129, 129, 126, 126,
133, 124, 134, 121, 136, 122, 137, 119, 137, 124, 128, 127, 129, 135, 117, 140,
118, 136, 123, 132, 128, 125, 134, 123, 132, 131, 121, 138, 121, 131, 127, 131,
123, 136, 123, 130, 135, 118, 137, 122, 134, 120, 140, 121, 130, 134, 120, 140,
119, 136, 127, 123, 139, 119, 134, 127, 130, 125, 129, 132, 122, 132, 126, 130,
126, 133, 125, 130, 128, 130, 125, 132, 126, 127, 132, 124, 134, 122, 132, 128,
127, 129, 129, 130, 127, 131, 124, 131, 130, 124, 134, 123, 129, 129, 130, 130,
122, 136, 124, 127, 135, 119, 137, 123, 130, 132, 122, 135, 123, 132, 129, 124,
132, 128, 125, 132, 125, 130, 128, 127, 129, 127, 131, 127, 129, 127, 131, 127,
127, 133, 123, 131, 130, 124, 134, 123, 133, 126, 127, 134, 120, 138, 122, 131,
135, 117, 143, 116, 135, 129, 121, 139, 122, 129, 130, 126, 126, 138, 112, 146,
113, 136, 132, 115, 145, 112, 135, 127, 128, 130, 127, 127, 133, 123, 132, 127,
131, 120, 135, 124, 131, 129, 123, 136, 119, 139, 118, 136, 125, 129, 129, 128,
129, 130, 126, 130, 129, 124, 136, 123, 131, 124, 135, 120, 132, 129, 124, 135,
121, 137, 120, 135, 127, 125, 135, 120, 136, 122, 133, 126, 125, 134, 121, 134,
126, 127, 131, 127, 127, 129, 129, 124, 135, 123, 128, 134, 119, 139, 117, 135,
128, 122, 137, 118, 137, 122, 130, 130, 124, 134, 125, 129, 128, 129, 127, 127,
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

#endif /* CR_H_ */
