wgd-modular/utf-8-samplified/firmware/jungle/OH.h

#ifndef OH_H_
#define OH_H_
 
const uint16_t OHLen = 3000; 
const uint8_t  OH[3000] PROGMEM = {128, 127, 128, 127, 128, 127, 128, 126, 129,
128, 128, 129, 125, 130, 126, 130, 132, 126, 126, 136, 121, 130, 118, 127, 126,
115, 145, 124, 136, 130, 131, 133, 117, 123, 120, 109, 131, 117, 133, 138, 107,
142, 120, 143, 141, 133, 142, 101, 150, 149, 88, 150, 100, 121, 139, 101, 178,
93, 108, 145, 80, 150, 128, 110, 173, 101, 189, 120, 105, 179, 108, 152, 103,
100, 128, 106, 162, 136, 84, 165, 102, 161, 175, 131, 178, 103, 87, 145, 81, 98,
136, 80, 159, 93, 172, 139, 122, 187, 81, 143, 111, 126, 126, 137, 185, 114, 91,
109, 109, 160, 136, 126, 161, 144, 125, 153, 121, 78, 123, 80, 128, 157, 119,
162, 150, 99, 132, 138, 156, 110, 135, 139, 50, 130, 130, 94, 116, 121, 133,
160, 160, 193, 131, 128, 143, 82, 171, 86, 160, 173, 61, 159, 60, 80, 95, 90,
135, 108, 148, 159, 188, 158, 161, 161, 143, 167, 123, 187, 104, 110, 74, 55,
60, 43, 154, 70, 155, 129, 168, 176, 133, 177, 152, 133, 130, 143, 119, 97, 130,
104, 50, 168, 40, 131, 156, 112, 189, 100, 145, 119, 113, 158, 125, 122, 179,
83, 159, 140, 127, 147, 92, 136, 105, 145, 116, 162, 113, 83, 124, 137, 77, 160,
152, 78, 179, 109, 153, 120, 104, 163, 130, 115, 188, 135, 161, 107, 110, 119,
36, 107, 78, 132, 90, 172, 132, 144, 145, 171, 168, 178, 148, 144, 197, 60, 188,
66, 83, 26, 119, 144, 66, 123, 118, 148, 111, 156, 180, 186, 147, 224, 160, 181,
135, 140, 126, 1, 168, 107, 19, 129, 59, 100, 122, 114, 164, 154, 189, 180, 213,
218, 178, 131, 131, 115, 107, 51, 136, 154, 35, 109, 101, 108, 74, 111, 168,
109, 191, 227, 146, 164, 187, 126, 138, 90, 128, 131, 100, 97, 107, 183, 136,
93, 131, 120, 110, 170, 131, 186, 146, 196, 132, 113, 194, 154, 186, 171, 168,
86, 96, 107, 158, 67, 95, 63, 110, 129, 118, 163, 101, 189, 112, 220, 168, 137,
233, 196, 128, 146, 128, 179, 171, 86, 116, 32, 132, 91, 133, 136, 131, 149,
164, 218, 234, 179, 170, 208, 86, 136, 79, 152, 80, 101, 141, 58, 113, 107, 144,
109, 133, 164, 188, 148, 149, 135, 165, 131, 111, 191, 111, 148, 158, 103, 84,
96, 119, 101, 94, 134, 142, 117, 162, 155, 187, 108, 161, 188, 126, 155, 97,
171, 133, 98, 133, 74, 97, 133, 70, 131, 109, 111, 183, 124, 169, 156, 167, 184,
170, 208, 113, 135, 147, 144, 140, 39, 99, 103, 114, 130, 124, 143, 166, 135,
177, 152, 153, 153, 150, 201, 65, 128, 114, 102, 118, 123, 151, 92, 94, 219,
105, 115, 187, 73, 177, 65, 176, 140, 99, 151, 139, 148, 103, 183, 163, 113,
117, 174, 72, 159, 102, 124, 93, 83, 166, 96, 165, 131, 162, 141, 135, 125, 178,
117, 149, 162, 90, 138, 110, 156, 70, 142, 113, 94, 182, 100, 175, 135, 105,
159, 93, 136, 149, 130, 180, 85, 155, 142, 67, 200, 79, 111, 143, 104, 165, 107,
159, 91, 88, 157, 99, 140, 175, 121, 190, 123, 125, 193, 75, 161, 126, 85, 126,
67, 141, 94, 59, 178, 83, 151, 154, 176, 211, 130, 185, 127, 131, 93, 86, 108,
60, 89, 129, 71, 106, 160, 100, 142, 144, 133, 139, 159, 162, 121, 137, 80, 140,
131, 87, 118, 116, 125, 91, 142, 169, 96, 137, 166, 109, 133, 94, 134, 130, 79,
117, 122, 111, 149, 139, 130, 144, 135, 157, 116, 162, 106, 101, 135, 82, 114,
109, 100, 116, 80, 179, 173, 112, 219, 123, 168, 152, 115, 168, 93, 102, 99, 87,
87, 100, 116, 104, 111, 157, 142, 163, 168, 154, 185, 107, 130, 170, 90, 131,
80, 116, 83, 76, 171, 92, 129, 129, 149, 128, 147, 162, 157, 119, 122, 126, 118,
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

#endif /* OH_H_ */
