wgd-modular/utf-8-samplified/firmware/jungle/RD.h

#ifndef RD_H_
#define RD_H_
 
const uint16_t RDLen = 3000; 
const uint8_t  RD[3000] PROGMEM = {127, 128, 127, 128, 128, 128, 128, 128, 128,
127, 129, 127, 130, 126, 130, 124, 132, 121, 141, 80, 6, 64, 62, 127, 97, 74,
160, 190, 244, 228, 255, 215, 255, 200, 194, 168, 97, 95, 3, 28, 17, 30, 18, 37,
8, 123, 56, 128, 183, 76, 102, 129, 138, 144, 212, 138, 200, 183, 233, 229, 223,
242, 217, 231, 221, 204, 179, 229, 128, 100, 177, 75, 49, 98, 42, 29, 34, 32,
25, 31, 30, 27, 46, 109, 171, 96, 101, 229, 142, 35, 133, 97, 188, 250, 181,
178, 178, 219, 215, 238, 163, 174, 234, 216, 168, 219, 162, 171, 197, 57, 31,
34, 33, 54, 62, 88, 148, 23, 108, 96, 56, 73, 22, 50, 22, 113, 58, 63, 79, 154,
198, 171, 205, 180, 232, 208, 219, 213, 211, 215, 205, 223, 150, 154, 130, 101,
163, 148, 69, 33, 43, 41, 64, 39, 43, 54, 91, 70, 43, 42, 74, 155, 117, 146,
167, 132, 181, 225, 183, 161, 209, 205, 215, 198, 157, 219, 197, 213, 169, 143,
87, 50, 50, 59, 112, 63, 137, 169, 162, 108, 91, 76, 51, 50, 54, 50, 54, 59, 92,
170, 179, 162, 148, 153, 80, 124, 173, 173, 205, 200, 203, 197, 205, 182, 202,
170, 120, 183, 114, 106, 111, 93, 146, 93, 141, 113, 88, 91, 52, 53, 68, 98, 55,
61, 57, 60, 66, 75, 101, 132, 160, 170, 187, 202, 193, 199, 194, 194, 199, 142,
168, 173, 139, 143, 131, 133, 154, 123, 114, 150, 129, 98, 63, 73, 72, 59, 76,
64, 65, 82, 147, 152, 95, 121, 120, 130, 127, 81, 98, 168, 172, 149, 175, 166,
172, 152, 174, 137, 137, 133, 119, 150, 145, 166, 148, 204, 173, 168, 142, 121,
116, 84, 91, 80, 66, 67, 65, 90, 83, 72, 122, 107, 123, 144, 141, 109, 151, 137,
152, 158, 110, 122, 143, 154, 162, 185, 156, 159, 189, 157, 162, 134, 112, 150,
129, 128, 104, 113, 100, 112, 124, 97, 83, 96, 111, 91, 75, 88, 142, 145, 144,
141, 131, 123, 135, 131, 134, 145, 120, 146, 128, 133, 149, 122, 142, 153, 156,
120, 139, 153, 151, 153, 118, 113, 128, 118, 100, 112, 119, 128, 116, 110, 131,
136, 118, 121, 111, 108, 128, 117, 106, 115, 114, 114, 139, 127, 134, 139, 150,
149, 139, 151, 145, 158, 142, 149, 148, 139, 147, 109, 103, 133, 115, 118, 110,
96, 95, 98, 121, 117, 134, 145, 138, 149, 132, 119, 119, 109, 129, 118, 127,
126, 131, 141, 124, 133, 139, 139, 129, 123, 135, 144, 144, 158, 123, 121, 121,
112, 132, 109, 117, 130, 131, 144, 141, 140, 146, 125, 118, 124, 103, 101, 98,
120, 127, 118, 123, 144, 140, 122, 110, 111, 137, 126, 137, 149, 156, 145, 135,
126, 134, 137, 119, 122, 126, 136, 136, 126, 121, 135, 126, 131, 133, 125, 128,
129, 126, 117, 118, 112, 110, 110, 112, 118, 111, 123, 138, 142, 136, 142, 143,
133, 143, 144, 135, 126, 131, 135, 122, 112, 118, 127, 128, 126, 128, 132, 144,
130, 133, 131, 124, 126, 121, 119, 121, 118, 126, 141, 129, 136, 121, 113, 108,
113, 121, 129, 133, 136, 136, 143, 134, 128, 136, 113, 125, 128, 128, 129, 130,
133, 141, 149, 134, 132, 128, 117, 131, 127, 124, 121, 119, 121, 115, 114, 120,
120, 127, 127, 124, 139, 130, 137, 125, 138, 133, 132, 129, 125, 125, 114, 133,
136, 134, 127, 140, 124, 133, 127, 122, 135, 135, 128, 121, 124, 128, 123, 119,
123, 119, 135, 122, 121, 116, 130, 131, 129, 130, 128, 136, 131, 138, 130, 132,
117, 124, 126, 124, 119, 121, 132, 133, 133, 132, 139, 125, 133, 132, 136, 127,
126, 129, 125, 122, 120, 126, 126, 129, 122, 127, 125, 131, 126, 124, 130, 124,
129, 128, 127, 121, 118, 125, 123, 132, 134, 137, 136, 132, 132, 135, 132, 128,
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

#endif /* RD_H_ */
