wgd-modular/utf-8-samplified/firmware/jungle/RS.h

#ifndef RS_H_
#define RS_H_
 
const uint16_t RSLen = 3000; 
const uint8_t  RS[3000] PROGMEM = {126, 130, 126, 131, 125, 132, 119, 154, 244,
239, 229, 43, 13, 70, 66, 99, 32, 28, 155, 169, 69, 104, 18, 135, 178, 9, 114,
221, 242, 230, 237, 228, 213, 183, 159, 89, 41, 1, 90, 165, 119, 85, 149, 252,
76, 21, 29, 83, 78, 73, 137, 44, 23, 32, 49, 75, 121, 161, 198, 215, 233, 223,
90, 123, 214, 117, 82, 194, 240, 129, 101, 151, 132, 106, 173, 168, 71, 39, 35,
116, 107, 22, 66, 114, 127, 128, 127, 146, 215, 175, 53, 27, 45, 103, 56, 33,
106, 143, 206, 212, 173, 207, 221, 216, 218, 215, 212, 210, 119, 27, 87, 107,
79, 44, 52, 46, 41, 39, 80, 160, 86, 39, 48, 133, 199, 169, 145, 162, 205, 217,
212, 212, 198, 158, 207, 167, 74, 37, 59, 170, 170, 121, 126, 180, 173, 176,
201, 170, 187, 141, 106, 77, 55, 56, 41, 53, 56, 101, 97, 84, 119, 150, 155,
146, 133, 122, 130, 138, 176, 207, 206, 207, 198, 179, 181, 184, 184, 157, 147,
167, 145, 74, 43, 61, 52, 64, 93, 123, 121, 73, 73, 140, 144, 101, 107, 117,
108, 122, 157, 174, 182, 184, 188, 170, 169, 187, 199, 199, 157, 123, 100, 70,
59, 67, 107, 157, 189, 145, 112, 159, 153, 129, 125, 150, 147, 114, 80, 58, 58,
58, 115, 148, 140, 113, 121, 138, 124, 160, 157, 157, 171, 172, 189, 173, 183,
190, 191, 187, 147, 120, 96, 120, 117, 96, 85, 59, 63, 60, 64, 93, 120, 145,
157, 187, 168, 157, 172, 125, 149, 163, 155, 125, 89, 119, 136, 132, 138, 138,
116, 129, 152, 166, 152, 135, 144, 148, 110, 92, 116, 135, 149, 146, 157, 143,
98, 81, 97, 115, 108, 92, 85, 117, 98, 87, 116, 135, 170, 176, 176, 149, 139,
159, 163, 156, 128, 114, 122, 135, 143, 129, 142, 141, 131, 127, 114, 107, 105,
117, 110, 110, 80, 65, 73, 87, 123, 147, 165, 179, 182, 154, 139, 141, 136, 121,
109, 123, 136, 119, 131, 127, 111, 129, 146, 137, 117, 130, 142, 138, 145, 129,
98, 102, 132, 139, 148, 138, 132, 130, 109, 108, 87, 94, 104, 114, 86, 90, 113,
111, 126, 144, 161, 154, 179, 184, 176, 156, 133, 138, 131, 121, 102, 106, 118,
101, 106, 115, 123, 120, 118, 110, 111, 123, 137, 131, 125, 115, 103, 126, 102,
118, 138, 168, 169, 149, 161, 124, 107, 113, 110, 114, 119, 135, 135, 131, 118,
118, 134, 139, 154, 142, 127, 141, 143, 121, 102, 86, 98, 115, 111, 115, 134,
153, 145, 119, 102, 102, 101, 117, 127, 139, 153, 127, 122, 146, 139, 133, 158,
163, 157, 152, 148, 134, 113, 108, 96, 103, 108, 103, 108, 111, 124, 145, 136,
118, 118, 122, 132, 135, 138, 129, 128, 128, 107, 123, 131, 150, 154, 138, 154,
138, 112, 102, 112, 113, 133, 134, 117, 136, 137, 121, 131, 141, 135, 142, 134,
131, 130, 126, 121, 105, 97, 89, 97, 111, 123, 141, 135, 137, 134, 131, 129,
116, 137, 156, 149, 129, 119, 122, 134, 145, 146, 137, 144, 146, 128, 114, 110,
104, 98, 99, 103, 113, 117, 127, 138, 135, 133, 134, 140, 138, 136, 141, 124,
129, 131, 117, 113, 112, 120, 127, 135, 146, 142, 130, 128, 127, 126, 120, 117,
130, 140, 126, 125, 130, 131, 139, 130, 120, 121, 131, 125, 115, 121, 122, 114,
101, 103, 111, 126, 141, 152, 137, 130, 147, 135, 130, 133, 121, 125, 132, 127,
133, 124, 116, 119, 134, 147, 131, 123, 126, 133, 126, 111, 108, 113, 121, 123,
115, 117, 140, 150, 142, 135, 136, 131, 120, 123, 122, 115, 119, 123, 122, 120,
121, 129, 123, 136, 148, 142, 138, 130, 138, 122, 118, 126, 121, 127, 116, 124,
132, 135, 128, 118, 126, 134, 128, 111, 117, 133, 125, 112, 116, 125, 124, 134,
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

#endif /* RS_H_ */
