wgd-modular/utf-8-samplified/firmware/jungle/SD.h

#ifndef SD_H_
#define SD_H_
 
const uint16_t SDLen = 3000; 
const uint8_t  SD[3000] PROGMEM = {128, 127, 129, 127, 129, 126, 129, 125, 130,
113, 64, 78, 101, 123, 132, 118, 119, 153, 231, 228, 223, 205, 197, 181, 160,
143, 60, 18, 32, 33, 44, 55, 68, 125, 132, 224, 220, 232, 116, 63, 225, 188,
185, 171, 136, 138, 106, 81, 93, 27, 103, 106, 17, 136, 143, 111, 4, 132, 214,
106, 163, 61, 131, 171, 166, 155, 35, 45, 82, 89, 101, 108, 132, 164, 203, 232,
231, 219, 219, 154, 198, 195, 99, 181, 187, 92, 20, 159, 98, 29, 107, 140, 52,
58, 115, 114, 130, 95, 167, 76, 112, 224, 156, 176, 241, 208, 111, 41, 97, 105,
94, 139, 144, 94, 207, 234, 190, 197, 169, 179, 80, 128, 80, 9, 59, 151, 107,
14, 70, 31, 111, 148, 126, 157, 121, 66, 98, 138, 119, 141, 146, 102, 78, 174,
255, 128, 119, 118, 105, 119, 103, 130, 66, 164, 223, 186, 169, 171, 115, 74,
48, 56, 75, 64, 72, 94, 127, 123, 161, 191, 162, 160, 223, 189, 145, 153, 158,
206, 175, 79, 103, 75, 92, 172, 162, 66, 104, 179, 138, 149, 93, 132, 94, 100,
194, 137, 142, 136, 123, 52, 83, 92, 84, 93, 57, 105, 133, 165, 185, 217, 204,
190, 176, 202, 142, 135, 181, 115, 55, 54, 94, 102, 115, 150, 108, 116, 166, 84,
133, 183, 143, 114, 109, 138, 169, 144, 170, 132, 84, 124, 80, 71, 66, 80, 108,
123, 162, 232, 206, 176, 185, 184, 159, 112, 94, 41, 79, 110, 66, 65, 93, 124,
98, 148, 145, 128, 164, 168, 171, 126, 160, 144, 172, 138, 134, 160, 58, 92,
112, 96, 66, 44, 59, 88, 97, 175, 180, 116, 187, 215, 216, 179, 155, 85, 102,
181, 73, 60, 95, 85, 79, 132, 108, 86, 126, 141, 208, 175, 173, 160, 124, 139,
175, 115, 101, 122, 81, 109, 83, 84, 144, 88, 107, 156, 114, 155, 167, 163, 153,
186, 176, 137, 125, 111, 104, 88, 81, 99, 94, 131, 132, 90, 167, 163, 142, 139,
178, 160, 137, 130, 117, 128, 81, 101, 92, 100, 105, 106, 174, 140, 112, 115,
127, 176, 140, 137, 145, 140, 173, 171, 151, 127, 101, 78, 95, 89, 109, 110, 75,
108, 162, 165, 155, 160, 155, 172, 158, 131, 110, 109, 105, 83, 112, 101, 74,
93, 111, 141, 149, 175, 127, 151, 157, 150, 173, 137, 157, 134, 138, 146, 117,
75, 93, 120, 94, 81, 122, 106, 113, 125, 172, 170, 142, 163, 160, 158, 132, 147,
94, 105, 118, 128, 112, 80, 106, 103, 121, 159, 149, 120, 146, 174, 182, 141,
149, 129, 99, 116, 103, 93, 96, 113, 118, 91, 106, 143, 114, 125, 149, 152, 161,
167, 166, 147, 149, 156, 110, 97, 102, 107, 101, 106, 113, 69, 124, 138, 131,
161, 157, 143, 149, 155, 143, 162, 129, 103, 76, 92, 109, 96, 115, 102, 127,
107, 112, 153, 136, 150, 168, 145, 166, 167, 153, 154, 102, 135, 128, 81, 90,
94, 107, 107, 103, 108, 122, 169, 146, 137, 166, 130, 127, 135, 137, 133, 115,
107, 130, 125, 121, 126, 127, 116, 126, 147, 143, 148, 145, 148, 147, 141, 135,
122, 113, 119, 94, 106, 121, 89, 100, 112, 113, 127, 115, 148, 155, 150, 159,
151, 146, 120, 127, 111, 113, 124, 92, 96, 112, 128, 131, 114, 132, 146, 151,
146, 166, 156, 140, 146, 131, 127, 107, 92, 89, 117, 101, 101, 113, 125, 125,
135, 148, 143, 148, 136, 170, 149, 153, 151, 123, 137, 114, 131, 122, 117, 114,
93, 115, 121, 133, 133, 139, 133, 150, 153, 148, 153, 121, 137, 120, 104, 117,
107, 97, 107, 115, 114, 123, 130, 130, 129, 145, 148, 148, 140, 130, 145, 128,
118, 118, 110, 124, 114, 110, 102, 109, 116, 118, 129, 130, 137, 126, 137, 148,
140, 142, 145, 119, 116, 136, 136, 116, 109, 108, 124, 120, 115, 140, 140, 147,
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

#endif /* SD_H_ */
