wgd-modular/utf-8-samplified/firmware/cavetechno/BD.h

#ifndef BD_H_
#define BD_H_
 
const uint16_t BDLen = 1374;

const uint8_t BD[1374] PROGMEM = {128, 128, 128, 128, 128, 128, 128, 128, 128,
127, 128, 127, 129, 127, 129, 117, 112, 125, 140, 147, 132, 157, 173, 173, 191,
182, 192, 192, 180, 192, 163, 147, 145, 117, 102, 89, 79, 69, 47, 45, 45, 37,
27, 35, 37, 29, 49, 45, 39, 60, 70, 83, 120, 148, 157, 153, 158, 182, 195, 200,
205, 204, 210, 217, 211, 199, 200, 197, 178, 170, 163, 160, 152, 142, 146, 152,
141, 129, 133, 135, 132, 124, 114, 111, 111, 108, 101, 100, 105, 104, 99, 97,
101, 106, 109, 110, 114, 119, 123, 126, 128, 132, 134, 137, 141, 139, 141, 147,
148, 150, 157, 162, 166, 174, 180, 189, 195, 193, 190, 189, 191, 198, 204, 200,
192, 190, 184, 178, 177, 177, 176, 169, 158, 148, 138, 123, 109, 94, 79, 65, 51,
39, 31, 24, 18, 13, 9, 10, 13, 16, 19, 22, 25, 27, 29, 31, 31, 32, 33, 33, 32,
34, 35, 36, 39, 43, 46, 50, 56, 62, 65, 67, 70, 74, 80, 88, 93, 97, 106, 119,
129, 138, 151, 165, 177, 188, 199, 213, 226, 232, 236, 245, 248, 244, 239, 234,
230, 226, 222, 219, 217, 215, 213, 212, 212, 211, 211, 211, 211, 211, 211, 210,
210, 210, 210, 211, 211, 213, 215, 217, 219, 222, 224, 227, 229, 231, 232, 232,
229, 223, 215, 206, 197, 187, 177, 166, 156, 147, 138, 128, 119, 111, 102, 92,
82, 73, 63, 53, 44, 35, 28, 21, 14, 9, 7, 6, 6, 8, 10, 12, 15, 17, 19, 21, 22,
24, 25, 27, 28, 29, 31, 32, 33, 35, 36, 38, 40, 41, 42, 44, 45, 46, 47, 48, 48,
50, 52, 56, 60, 65, 71, 76, 83, 88, 94, 98, 103, 107, 110, 112, 114, 115, 116,
116, 116, 116, 117, 117, 118, 119, 121, 123, 126, 129, 132, 135, 138, 141, 144,
147, 149, 151, 153, 155, 156, 158, 159, 161, 163, 164, 167, 169, 171, 174, 177,
180, 183, 186, 189, 192, 195, 198, 201, 204, 207, 210, 213, 215, 218, 219, 221,
223, 224, 224, 225, 225, 225, 225, 224, 223, 222, 220, 219, 217, 215, 213, 211,
210, 208, 206, 204, 202, 201, 200, 198, 197, 196, 196, 195, 195, 195, 195, 195,
195, 195, 194, 194, 193, 191, 190, 188, 186, 183, 181, 178, 175, 171, 168, 165,
162, 158, 155, 152, 149, 145, 142, 139, 135, 132, 128, 124, 120, 117, 112, 108,
104, 100, 96, 91, 87, 83, 78, 73, 69, 64, 60, 55, 51, 47, 43, 39, 36, 34, 33,
32, 32, 33, 34, 35, 37, 39, 41, 43, 45, 47, 49, 51, 52, 54, 56, 57, 59, 60, 61,
62, 64, 65, 66, 67, 68, 68, 69, 69, 70, 70, 70, 70, 71, 71, 70, 70, 70, 70, 69,
69, 68, 67, 67, 66, 66, 66, 66, 67, 69, 71, 74, 77, 81, 86, 90, 95, 100, 106,
111, 116, 121, 126, 131, 136, 141, 146, 151, 156, 161, 166, 171, 176, 181, 185,
190, 195, 199, 203, 206, 209, 210, 212, 212, 212, 211, 210, 209, 207, 205, 203,
201, 199, 198, 196, 195, 193, 192, 191, 189, 188, 187, 186, 185, 184, 183, 183,
182, 181, 181, 180, 180, 180, 180, 180, 179, 179, 179, 179, 179, 179, 179, 179,
179, 179, 179, 180, 180, 181, 181, 181, 182, 182, 183, 183, 182, 181, 179, 176,
172, 168, 163, 158, 153, 147, 141, 135, 129, 124, 118, 113, 108, 103, 99, 95,
90, 87, 83, 80, 77, 73, 71, 68, 65, 63, 61, 59, 57, 56, 56, 56, 56, 56, 57, 58,
59, 61, 62, 64, 65, 66, 67, 69, 70, 71, 72, 72, 73, 74, 74, 75, 75, 76, 76, 76,
76, 77, 77, 77, 77, 77, 77, 77, 77, 77, 77, 77, 77, 77, 77, 77, 78, 78, 78, 78,
78, 79, 79, 79, 79, 80, 80, 80, 81, 81, 81, 81, 82, 82, 83, 85, 86, 88, 91, 94,
97, 101, 105, 109, 113, 117, 122, 126, 130, 134, 138, 142, 146, 149, 152, 155,
157, 159, 162, 164, 165, 167, 169, 171, 173, 175, 176, 178, 180, 182, 183, 184,
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

#endif /* BD_H_ */
