wgd-modular/utf-8-samplified/firmware/cavetechno/CR.h

#ifndef CR_H_
#define CR_H_
 
const uint16_t CRLen = 1800;

const uint8_t CR[1800] PROGMEM = {131, 125, 129, 127, 127, 130, 123, 134, 119,
139, 114, 145, 107, 157, 101, 164, 100, 160, 113, 128, 143, 86, 151, 82, 144,
85, 133, 90, 126, 95, 120, 102, 115, 109, 111, 113, 111, 118, 110, 122, 111,
125, 112, 126, 113, 127, 116, 128, 117, 127, 119, 127, 121, 127, 123, 127, 125,
127, 126, 127, 127, 127, 129, 127, 130, 127, 130, 128, 130, 128, 131, 130, 132,
130, 131, 130, 131, 131, 132, 131, 132, 130, 133, 130, 133, 129, 133, 129, 133,
130, 134, 131, 133, 131, 133, 132, 132, 134, 130, 135, 129, 136, 127, 137, 126,
138, 125, 139, 124, 139, 124, 139, 124, 139, 124, 139, 125, 137, 127, 136, 131,
132, 136, 128, 142, 123, 146, 118, 151, 109, 154, 105, 157, 104, 161, 103, 162,
106, 157, 108, 149, 115, 141, 127, 130, 142, 114, 155, 97, 171, 86, 187, 72,
193, 63, 197, 65, 195, 72, 182, 87, 164, 112, 136, 139, 103, 173, 72, 202, 43,
226, 26, 237, 20, 235, 33, 214, 61, 177, 104, 128, 156, 78, 206, 31, 243, 3,
255, 0, 254, 19, 218, 68, 161, 128, 96, 194, 36, 244, 0, 255, 0, 247, 31, 197,
94, 125, 169, 53, 231, 8, 255, 1, 240, 40, 182, 112, 104, 192, 33, 246, 0, 253,
19, 207, 87, 126, 172, 43, 239, 0, 255, 16, 209, 87, 122, 180, 36, 246, 0, 251,
31, 190, 118, 92, 211, 14, 255, 2, 224, 67, 132, 170, 38, 248, 1, 249, 46, 164,
144, 53, 234, 0, 253, 37, 177, 138, 59, 232, 0, 252, 39, 171, 143, 50, 239, 0,
248, 51, 145, 166, 34, 255, 2, 223, 79, 110, 209, 9, 252, 20, 188, 136, 54, 240,
2, 237, 66, 118, 203, 11, 252, 24, 179, 147, 41, 253, 4, 214, 100, 88, 225, 0,
247, 60, 120, 205, 6, 250, 42, 149, 177, 24, 253, 23, 175, 155, 32, 255, 12,
188, 146, 38, 255, 9, 191, 144, 39, 255, 10, 189, 146, 36, 255, 13, 180, 156,
29, 252, 28, 157, 178, 17, 250, 47, 131, 206, 3, 243, 71, 97, 227, 1, 219, 112,
60, 249, 12, 182, 159, 22, 252, 41, 131, 209, 3, 231, 94, 69, 245, 10, 181, 162,
19, 250, 55, 109, 223, 2, 211, 131, 38, 251, 35, 133, 211, 2, 221, 118, 46, 251,
33, 137, 209, 2, 219, 125, 40, 250, 44, 120, 221, 4, 202, 149, 23, 247, 69, 86,
241, 16, 163, 191, 7, 224, 119, 41, 249, 52, 104, 233, 12, 172, 184, 8, 224,
121, 37, 247, 62, 88, 240, 20, 148, 208, 7, 201, 159, 18, 234, 107, 47, 247, 59,
88, 241, 27, 138, 220, 11, 178, 184, 7, 210, 147, 23, 235, 109, 42, 244, 75, 72,
247, 49, 100, 236, 29, 132, 224, 16, 157, 205, 12, 181, 185, 9, 200, 167, 13,
213, 148, 22, 225, 130, 28, 233, 116, 35, 238, 105, 43, 239, 96, 49, 241, 89,
55, 241, 84, 58, 242, 83, 60, 241, 82, 60, 241, 84, 57, 241, 88, 53, 239, 95,
49, 238, 104, 42, 233, 114, 35, 227, 128, 28, 220, 144, 22, 210, 160, 18, 195,
179, 16, 177, 197, 19, 155, 213, 28, 130, 228, 41, 104, 236, 61, 77, 238, 88,
52, 230, 120, 32, 215, 154, 20, 189, 187, 21, 154, 214, 35, 115, 231, 61, 76,
235, 99, 44, 221, 143, 24, 190, 186, 24, 146, 219, 44, 97, 233, 84, 54, 223,
135, 27, 190, 186, 26, 139, 222, 54, 84, 231, 105, 41, 208, 164, 26, 158, 211,
44, 98, 230, 95, 47, 210, 159, 27, 157, 211, 49, 92, 227, 106, 41, 200, 174, 31,
137, 219, 68, 69, 220, 137, 32, 170, 201, 46, 98, 224, 107, 42, 191, 182, 37,
119, 222, 90, 52, 201, 167, 35, 131, 218, 82, 59, 204, 162, 37, 134, 216, 83,
60, 202, 165, 39, 129, 217, 91, 54, 194, 174, 43, 116, 217, 107, 47, 179, 189,
55, 94, 213, 131, 42, 154, 204, 76, 70, 199, 163, 45, 120, 213, 108, 49, 171,
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
};

#endif /* CR_H_ */
