wgd-modular/utf-8-samplified/firmware/cavetechno/OH.h

#ifndef OH_H_
#define OH_H_
 
const uint16_t OHLen = 1447;

const uint8_t OH[1447] PROGMEM = {126, 130, 127, 128, 128, 127, 130, 125, 133,
121, 137, 115, 146, 115, 146, 132, 150, 166, 80, 136, 126, 51, 198, 149, 101,
111, 116, 157, 29, 200, 96, 110, 133, 98, 171, 127, 119, 116, 130, 120, 159, 85,
126, 120, 156, 90, 135, 156, 69, 142, 128, 147, 79, 142, 127, 138, 74, 99, 182,
126, 86, 90, 192, 80, 128, 177, 71, 101, 169, 96, 157, 125, 108, 95, 154, 179,
65, 160, 109, 125, 120, 153, 103, 120, 178, 99, 135, 113, 105, 150, 127, 101,
128, 147, 162, 102, 110, 138, 137, 119, 105, 146, 139, 121, 115, 141, 129, 98,
124, 160, 124, 104, 113, 122, 135, 131, 140, 101, 139, 120, 116, 130, 109, 152,
122, 112, 122, 114, 155, 118, 112, 152, 77, 147, 160, 96, 135, 128, 111, 125,
123, 136, 154, 108, 99, 140, 154, 98, 114, 148, 130, 137, 100, 118, 161, 115,
122, 123, 105, 162, 126, 117, 120, 129, 128, 124, 149, 121, 113, 103, 162, 131,
111, 133, 117, 130, 130, 136, 106, 141, 125, 109, 171, 108, 117, 127, 129, 132,
124, 143, 99, 155, 115, 136, 137, 112, 145, 110, 144, 149, 100, 123, 145, 127,
133, 104, 146, 123, 113, 142, 140, 132, 98, 126, 161, 112, 134, 126, 107, 156,
117, 114, 133, 139, 138, 120, 100, 154, 131, 124, 130, 114, 144, 124, 133, 121,
128, 145, 111, 137, 131, 105, 153, 104, 118, 158, 123, 117, 127, 128, 135, 114,
122, 148, 113, 150, 110, 115, 140, 123, 154, 111, 130, 122, 121, 128, 124, 150,
106, 138, 127, 118, 150, 108, 124, 145, 124, 136, 119, 115, 153, 135, 97, 138,
157, 109, 124, 149, 110, 127, 149, 127, 127, 97, 150, 149, 103, 133, 145, 109,
114, 153, 142, 106, 138, 138, 118, 140, 141, 115, 118, 148, 114, 138, 130, 131,
120, 135, 127, 107, 145, 136, 144, 103, 117, 151, 123, 119, 139, 120, 128, 118,
127, 141, 126, 131, 134, 122, 114, 145, 135, 130, 113, 130, 137, 140, 124, 110,
141, 129, 127, 136, 131, 125, 135, 107, 138, 150, 106, 139, 132, 110, 142, 137,
112, 131, 133, 124, 123, 135, 127, 117, 136, 130, 130, 115, 145, 127, 113, 143,
126, 136, 115, 127, 142, 135, 109, 125, 149, 128, 122, 111, 131, 148, 133, 105,
141, 134, 111, 134, 134, 136, 124, 124, 122, 136, 129, 128, 137, 114, 138, 127,
133, 133, 115, 131, 134, 127, 130, 135, 124, 137, 113, 139, 130, 123, 141, 110,
144, 125, 124, 131, 131, 130, 118, 141, 129, 119, 127, 130, 130, 138, 130, 119,
125, 132, 124, 137, 126, 124, 132, 128, 130, 125, 131, 127, 126, 129, 132, 127,
125, 127, 136, 119, 134, 127, 132, 126, 123, 134, 125, 139, 113, 137, 129, 129,
122, 120, 140, 139, 124, 119, 133, 122, 134, 127, 136, 124, 129, 127, 126, 137,
116, 132, 133, 124, 132, 129, 130, 125, 126, 131, 130, 126, 129, 132, 122, 130,
125, 133, 132, 129, 124, 127, 131, 130, 133, 122, 129, 124, 129, 134, 132, 123,
127, 131, 127, 134, 125, 126, 131, 129, 128, 125, 129, 135, 126, 125, 129, 132,
128, 129, 126, 127, 135, 127, 128, 127, 129, 126, 133, 129, 125, 128, 128, 133,
126, 127, 126, 132, 126, 130, 131, 129, 128, 121, 133, 130, 128, 127, 130, 132,
127, 125, 125, 133, 133, 126, 127, 128, 130, 125, 130, 130, 128, 130, 128, 127,
128, 132, 125, 127, 129, 130, 127, 129, 129, 129, 131, 124, 128, 130, 128, 130,
130, 129, 124, 127, 131, 127, 131, 128, 131, 127, 128, 127, 128, 130, 129, 129,
127, 127, 127, 132, 126, 129, 129, 128, 130, 127, 129, 126, 131, 128, 125, 131,
130, 127, 127, 130, 127, 130, 129, 126, 128, 129, 131, 127, 127, 128, 129, 128,
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

#endif /* OH_H_ */
