wgd-modular/utf-8-samplified/firmware/cavetechno/RD.h

#ifndef RD_H_
#define RD_H_
 
const uint16_t RDLen = 1544;

const uint8_t RD[1544] PROGMEM = {128, 128, 128, 127, 128, 127, 128, 127, 129,
123, 111, 102, 133, 132, 138, 159, 125, 139, 154, 118, 122, 151, 114, 82, 135,
136, 99, 165, 124, 123, 120, 149, 126, 99, 169, 69, 136, 136, 108, 137, 134,
134, 101, 173, 126, 84, 186, 111, 145, 155, 111, 139, 98, 152, 75, 136, 134, 82,
176, 120, 137, 120, 124, 139, 100, 162, 115, 138, 164, 124, 158, 133, 137, 117,
128, 143, 99, 155, 131, 117, 144, 130, 138, 113, 141, 108, 118, 132, 114, 134,
119, 127, 125, 139, 127, 131, 131, 109, 134, 121, 128, 136, 134, 122, 133, 154,
136, 140, 143, 125, 121, 124, 133, 127, 115, 127, 122, 140, 131, 146, 139, 124,
115, 127, 126, 108, 132, 106, 121, 137, 143, 161, 152, 143, 115, 136, 140, 93,
138, 110, 99, 136, 138, 156, 124, 155, 138, 119, 153, 113, 133, 106, 119, 112,
102, 144, 111, 127, 141, 117, 131, 128, 125, 124, 108, 149, 128, 140, 154, 143,
148, 132, 142, 126, 116, 127, 103, 120, 119, 123, 131, 114, 142, 121, 139, 146,
123, 144, 122, 133, 126, 129, 129, 101, 141, 108, 127, 136, 115, 142, 126, 144,
128, 144, 152, 112, 159, 121, 125, 130, 116, 138, 92, 141, 101, 119, 148, 101,
152, 103, 137, 126, 117, 163, 91, 144, 112, 134, 139, 118, 167, 96, 141, 137,
120, 145, 103, 159, 101, 130, 149, 109, 162, 106, 146, 109, 126, 146, 93, 153,
94, 116, 141, 115, 149, 106, 165, 115, 123, 156, 103, 141, 109, 132, 114, 122,
157, 103, 148, 126, 125, 139, 115, 137, 102, 141, 109, 131, 138, 115, 140, 125,
134, 119, 133, 118, 101, 135, 110, 130, 128, 130, 130, 119, 150, 112, 150, 132,
128, 131, 116, 142, 116, 145, 130, 117, 138, 106, 149, 117, 124, 121, 101, 131,
116, 148, 124, 130, 142, 113, 140, 140, 123, 116, 123, 129, 106, 150, 130, 115,
129, 127, 125, 121, 141, 120, 118, 143, 123, 132, 133, 124, 120, 124, 129, 109,
130, 130, 116, 124, 130, 130, 131, 131, 135, 126, 136, 124, 126, 124, 112, 133,
127, 106, 128, 115, 141, 128, 134, 142, 111, 143, 115, 141, 129, 112, 144, 110,
134, 118, 123, 135, 87, 150, 100, 131, 135, 116, 156, 109, 159, 117, 142, 150,
95, 170, 104, 126, 120, 108, 129, 83, 162, 96, 120, 148, 105, 156, 125, 150,
114, 129, 161, 86, 171, 114, 115, 126, 114, 145, 83, 152, 98, 105, 143, 91, 158,
115, 141, 127, 123, 162, 95, 162, 118, 130, 129, 116, 150, 91, 144, 118, 110,
139, 94, 152, 102, 137, 136, 123, 153, 109, 154, 126, 130, 136, 125, 137, 110,
117, 131, 107, 133, 110, 127, 113, 123, 126, 118, 138, 120, 136, 131, 129, 135,
138, 138, 121, 124, 133, 120, 123, 120, 121, 102, 124, 129, 135, 124, 135, 132,
128, 146, 138, 140, 125, 122, 130, 114, 132, 118, 118, 115, 117, 132, 116, 149,
117, 126, 126, 132, 124, 132, 135, 111, 133, 132, 124, 128, 138, 129, 120, 141,
125, 118, 132, 119, 123, 123, 128, 115, 127, 137, 113, 140, 125, 120, 130, 127,
139, 123, 144, 114, 133, 140, 118, 132, 120, 118, 109, 121, 125, 102, 137, 118,
126, 143, 135, 146, 127, 150, 117, 148, 136, 110, 136, 112, 127, 102, 126, 120,
94, 144, 106, 151, 129, 126, 145, 114, 152, 121, 146, 130, 106, 153, 116, 136,
131, 111, 123, 97, 135, 101, 139, 124, 103, 150, 121, 138, 134, 143, 133, 108,
164, 116, 131, 139, 109, 128, 106, 143, 107, 133, 131, 106, 147, 114, 135, 135,
126, 136, 115, 156, 115, 136, 137, 114, 139, 116, 127, 120, 125, 123, 115, 136,
116, 118, 134, 117, 138, 122, 146, 131, 128, 139, 118, 143, 119, 124, 128, 110,
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

#endif /* RD_H_ */
