wgd-modular/utf-8-samplified/firmware/cavetechno/RS.h

#ifndef RS_H_
#define RS_H_
 
const uint16_t RSLen = 1608;

const uint8_t RS[1608] PROGMEM = {128, 128, 128, 127, 129, 126, 130, 125, 132,
120, 158, 141, 124, 186, 177, 107, 90, 174, 96, 31, 81, 38, 7, 50, 63, 63, 145,
203, 211, 242, 249, 247, 246, 247, 224, 170, 127, 82, 43, 14, 6, 9, 9, 9, 24,
63, 105, 143, 170, 194, 209, 216, 230, 225, 204, 186, 167, 140, 115, 98, 80, 61,
45, 48, 50, 61, 85, 99, 117, 151, 177, 203, 222, 221, 221, 220, 204, 183, 158,
119, 71, 36, 19, 10, 9, 25, 57, 87, 121, 166, 199, 220, 244, 249, 236, 224, 207,
179, 148, 110, 72, 48, 38, 27, 17, 24, 34, 49, 75, 101, 132, 161, 189, 219, 230,
235, 235, 223, 203, 175, 138, 103, 78, 50, 23, 16, 20, 28, 50, 79, 110, 150,
187, 213, 230, 240, 244, 233, 213, 188, 159, 124, 91, 59, 37, 23, 14, 21, 34,
49, 70, 97, 123, 154, 179, 199, 222, 232, 227, 221, 207, 187, 164, 137, 105, 72,
51, 34, 24, 27, 38, 54, 78, 112, 150, 183, 211, 229, 233, 230, 216, 194, 167,
136, 102, 70, 43, 24, 17, 20, 32, 53, 83, 113, 149, 185, 212, 228, 241, 240,
226, 210, 186, 159, 128, 96, 62, 33, 17, 14, 17, 28, 49, 74, 110, 149, 181, 213,
239, 243, 241, 234, 214, 189, 158, 119, 85, 59, 31, 14, 16, 22, 37, 62, 86, 116,
149, 179, 203, 218, 226, 228, 217, 202, 186, 163, 137, 110, 84, 59, 37, 27, 29,
35, 48, 68, 92, 123, 153, 183, 210, 228, 233, 229, 216, 195, 168, 134, 98, 66,
43, 30, 23, 29, 45, 63, 90, 121, 147, 181, 210, 222, 226, 223, 213, 194, 170,
148, 126, 104, 80, 58, 46, 43, 45, 48, 57, 77, 98, 119, 148, 175, 196, 211, 212,
210, 207, 191, 171, 143, 107, 74, 51, 31, 28, 35, 42, 64, 92, 126, 164, 194,
221, 234, 232, 230, 217, 197, 167, 139, 107, 72, 48, 28, 23, 25, 32, 48, 71, 96,
126, 159, 180, 199, 217, 221, 218, 212, 196, 174, 155, 127, 99, 73, 49, 40, 42,
43, 55, 76, 95, 121, 147, 173, 199, 215, 218, 216, 206, 190, 170, 144, 118, 93,
70, 52, 44, 48, 52, 61, 82, 102, 121, 146, 173, 194, 207, 213, 213, 206, 191,
169, 145, 119, 90, 63, 44, 36, 34, 39, 50, 71, 98, 135, 170, 197, 222, 227, 224,
219, 205, 180, 146, 116, 82, 53, 35, 31, 30, 38, 59, 80, 104, 137, 166, 192,
211, 216, 223, 218, 200, 185, 168, 144, 120, 98, 76, 57, 47, 41, 41, 51, 64, 80,
103, 133, 163, 189, 206, 217, 218, 212, 200, 181, 157, 129, 101, 70, 47, 37, 33,
39, 55, 71, 95, 127, 157, 183, 203, 216, 221, 218, 207, 191, 169, 145, 118, 88,
64, 50, 41, 40, 48, 57, 75, 99, 123, 150, 174, 194, 208, 214, 207, 201, 189,
169, 143, 118, 92, 64, 49, 43, 40, 46, 62, 83, 107, 137, 165, 188, 209, 216,
213, 208, 196, 173, 149, 120, 93, 67, 44, 40, 40, 44, 60, 82, 101, 125, 153,
174, 192, 209, 217, 215, 208, 195, 179, 155, 125, 101, 79, 56, 43, 42, 43, 48,
65, 87, 107, 133, 164, 188, 204, 213, 214, 207, 195, 175, 150, 127, 99, 73, 58,
48, 42, 48, 61, 73, 94, 120, 146, 170, 190, 205, 212, 209, 200, 190, 170, 148,
125, 101, 82, 63, 52, 50, 52, 63, 76, 94, 115, 141, 164, 182, 198, 206, 206,
200, 188, 168, 144, 117, 89, 68, 53, 47, 46, 54, 70, 89, 113, 141, 166, 186,
200, 207, 207, 201, 186, 170, 151, 127, 106, 87, 69, 60, 54, 55, 62, 72, 85,
106, 130, 151, 173, 189, 199, 204, 202, 193, 178, 160, 137, 109, 83, 64, 53, 50,
52, 59, 73, 92, 114, 141, 165, 186, 201, 208, 206, 200, 190, 172, 151, 128, 103,
83, 70, 59, 55, 57, 63, 76, 91, 109, 132, 154, 170, 184, 191, 193, 191, 184,
172, 157, 137, 116, 97, 79, 66, 60, 59, 64, 75, 93, 112, 135, 160, 178, 191,
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

#endif /* RS_H_ */
