wgd-modular/utf-8-samplified/firmware/cavetechno/SD.h

#ifndef SD_H_
#define SD_H_
 
const uint16_t SDLen = 1481;

const uint8_t SD[1481] PROGMEM = {129, 127, 129, 127, 129, 126, 130, 126, 131,
125, 131, 124, 133, 121, 138, 103, 41, 71, 102, 117, 86, 164, 195, 224, 211,
218, 204, 184, 153, 109, 65, 31, 51, 40, 52, 38, 107, 81, 162, 115, 95, 140,
129, 183, 151, 177, 190, 216, 202, 218, 197, 214, 177, 189, 174, 100, 160, 73,
86, 80, 40, 61, 40, 56, 42, 57, 74, 167, 94, 143, 189, 70, 113, 123, 206, 197,
152, 188, 192, 218, 157, 178, 214, 166, 193, 151, 184, 106, 44, 54, 61, 69, 108,
111, 67, 119, 70, 76, 47, 58, 95, 80, 73, 137, 178, 171, 182, 192, 205, 191,
203, 187, 203, 181, 147, 135, 112, 158, 115, 52, 60, 62, 73, 51, 77, 92, 74, 51,
94, 142, 125, 161, 132, 184, 194, 154, 189, 193, 194, 160, 189, 193, 179, 145,
97, 63, 67, 102, 90, 138, 167, 120, 99, 80, 65, 68, 68, 68, 83, 143, 175, 145,
154, 104, 121, 168, 171, 196, 178, 195, 171, 191, 152, 143, 147, 109, 109, 117,
122, 121, 123, 93, 88, 59, 88, 93, 69, 74, 72, 81, 93, 127, 152, 165, 183, 183,
184, 179, 188, 151, 156, 159, 134, 136, 132, 146, 114, 138, 134, 92, 81, 82, 78,
81, 80, 81, 146, 131, 109, 124, 129, 119, 87, 149, 163, 148, 167, 156, 156, 154,
135, 132, 126, 143, 150, 151, 177, 168, 147, 129, 113, 97, 94, 82, 76, 85, 97,
85, 117, 115, 132, 141, 118, 145, 137, 155, 116, 128, 145, 153, 172, 147, 168,
161, 152, 126, 128, 141, 120, 115, 109, 113, 123, 99, 95, 112, 101, 83, 119,
145, 139, 139, 124, 132, 129, 139, 131, 134, 132, 134, 138, 127, 155, 137, 128,
145, 149, 141, 114, 126, 119, 107, 118, 126, 120, 116, 137, 122, 122, 112, 120,
124, 110, 119, 114, 131, 131, 131, 143, 144, 141, 142, 149, 142, 145, 140, 143,
121, 109, 130, 117, 117, 103, 101, 114, 121, 132, 140, 140, 136, 122, 118, 120,
125, 124, 128, 135, 129, 130, 138, 134, 123, 135, 138, 150, 132, 122, 118, 124,
120, 118, 130, 135, 140, 138, 139, 120, 124, 111, 103, 112, 128, 119, 129, 142,
127, 113, 120, 133, 129, 148, 146, 140, 126, 134, 131, 121, 126, 133, 134, 122,
131, 128, 131, 129, 126, 130, 124, 120, 117, 114, 113, 118, 117, 123, 139, 135,
138, 139, 134, 142, 135, 127, 131, 130, 115, 121, 127, 128, 126, 134, 137, 130,
131, 125, 126, 121, 123, 120, 131, 134, 131, 125, 113, 114, 120, 129, 133, 134,
139, 133, 131, 126, 119, 131, 125, 131, 129, 141, 141, 132, 128, 121, 130, 126,
123, 122, 120, 117, 119, 123, 127, 126, 131, 135, 129, 132, 133, 131, 127, 127,
119, 130, 136, 129, 134, 129, 130, 125, 130, 135, 125, 124, 127, 124, 122, 123,
128, 127, 118, 124, 131, 130, 129, 131, 133, 133, 133, 125, 122, 127, 124, 120,
129, 133, 131, 135, 130, 129, 134, 130, 127, 128, 125, 122, 125, 127, 127, 125,
127, 129, 126, 127, 127, 127, 129, 124, 121, 124, 127, 132, 135, 135, 131, 132,
133, 128, 126, 132, 129, 130, 124, 126, 127, 122, 118, 123, 126, 125, 134, 132,
132, 129, 129, 125, 125, 125, 125, 127, 129, 129, 127, 129, 130, 129, 128, 131,
134, 133, 126, 124, 125, 123, 122, 129, 131, 132, 128, 127, 131, 126, 128, 127,
126, 122, 126, 129, 125, 125, 125, 129, 130, 130, 130, 131, 130, 130, 131, 128,
130, 128, 126, 125, 123, 125, 130, 129, 128, 129, 130, 127, 127, 126, 122, 123,
127, 127, 129, 133, 129, 129, 128, 130, 130, 129, 130, 129, 128, 123, 123, 127,
127, 128, 130, 132, 130, 128, 127, 126, 126, 126, 127, 128, 130, 127, 128, 123,
124, 128, 127, 129, 131, 131, 131, 131, 128, 126, 124, 127, 126, 128, 131, 131,
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

#endif /* SD_H_ */
