wgd-modular/utf-8-samplified/firmware/dilectro/RS.h

#ifndef RS_H_
#define RS_H_
 
const uint16_t RSLen = 1285;

const uint8_t RS[1285] PROGMEM = {128, 128, 128, 128, 127, 126, 125, 124, 122,
121, 120, 119, 119, 118, 118, 118, 117, 118, 116, 117, 117, 116, 117, 117, 117,
116, 117, 117, 117, 117, 117, 117, 118, 117, 118, 118, 118, 119, 119, 119, 120,
120, 121, 121, 122, 121, 122, 121, 123, 123, 122, 123, 123, 125, 123, 126, 123,
127, 124, 127, 123, 129, 125, 130, 125, 130, 126, 131, 127, 131, 130, 130, 131,
130, 132, 129, 136, 128, 138, 126, 142, 124, 145, 123, 148, 121, 149, 122, 146,
128, 140, 138, 125, 158, 105, 177, 89, 187, 92, 173, 123, 128, 173, 83, 203, 79,
175, 135, 107, 191, 89, 160, 159, 85, 200, 107, 124, 192, 84, 159, 172, 80, 177,
159, 81, 188, 150, 85, 186, 157, 81, 181, 171, 81, 161, 193, 89, 129, 208, 120,
93, 197, 171, 79, 146, 211, 119, 87, 188, 191, 88, 112, 207, 188, 95, 122, 210,
183, 100, 130, 209, 186, 109, 126, 203, 192, 124, 113, 188, 200, 147, 103, 156,
202, 175, 117, 111, 180, 193, 158, 101, 122, 183, 186, 147, 97, 116, 176, 182,
147, 98, 100, 159, 180, 153, 107, 83, 126, 169, 161, 125, 84, 84, 134, 161, 147,
114, 76, 77, 121, 150, 141, 114, 73, 57, 85, 130, 139, 124, 89, 52, 52, 90, 129,
130, 114, 76, 43, 46, 85, 123, 126, 112, 80, 44, 38, 66, 108, 125, 118, 99, 63,
38, 43, 74, 111, 123, 118, 101, 68, 43, 43, 66, 102, 123, 123, 113, 90, 60, 47,
54, 80, 111, 128, 127, 120, 100, 73, 56, 57, 74, 102, 126, 133, 131, 123, 102,
78, 65, 65, 78, 102, 126, 137, 138, 135, 122, 100, 82, 74, 76, 89, 111, 132,
143, 146, 146, 137, 120, 102, 90, 85, 88, 102, 122, 141, 151, 156, 157, 151,
138, 122, 108, 99, 97, 102, 117, 135, 151, 161, 167, 169, 166, 156, 142, 128,
116, 109, 107, 113, 127, 143, 158, 168, 175, 179, 178, 172, 160, 147, 134, 124,
117, 115, 119, 130, 145, 160, 171, 180, 186, 190, 188, 182, 172, 159, 147, 136,
127, 122, 123, 128, 139, 152, 165, 176, 185, 191, 195, 195, 191, 182, 172, 160,
148, 138, 129, 124, 123, 127, 135, 147, 159, 171, 181, 190, 196, 200, 201, 199,
193, 184, 173, 161, 150, 139, 131, 125, 122, 123, 128, 137, 147, 159, 169, 179,
187, 193, 198, 200, 199, 195, 188, 179, 168, 157, 146, 136, 127, 119, 115, 114,
116, 121, 129, 139, 150, 161, 171, 180, 189, 196, 202, 200, 198, 195, 193, 191,
189, 186, 178, 166, 154, 143, 133, 124, 117, 113, 111, 111, 114, 119, 125, 132,
139, 146, 152, 158, 163, 165, 163, 161, 159, 157, 155, 154, 151, 143, 131, 120,
108, 96, 85, 75, 66, 58, 52, 49, 47, 48, 50, 54, 60, 67, 74, 81, 88, 95, 101,
107, 112, 116, 119, 120, 121, 119, 116, 112, 106, 99, 92, 83, 74, 65, 56, 47,
40, 33, 27, 23, 20, 20, 21, 23, 27, 32, 39, 46, 54, 62, 70, 79, 87, 95, 102,
108, 114, 119, 123, 126, 127, 128, 127, 125, 122, 117, 112, 106, 100, 93, 86,
79, 72, 66, 60, 54, 50, 47, 45, 47, 49, 51, 53, 55, 58, 64, 71, 79, 87, 96, 105,
114, 122, 131, 138, 146, 153, 159, 164, 169, 172, 175, 177, 177, 177, 175, 173,
170, 165, 161, 155, 149, 143, 136, 129, 123, 116, 110, 104, 99, 94, 91, 88, 85,
84, 84, 85, 86, 89, 92, 97, 102, 108, 114, 121, 128, 135, 143, 150, 157, 164,
171, 177, 182, 188, 192, 196, 200, 202, 204, 206, 206, 206, 205, 204, 201, 199,
195, 191, 187, 182, 177, 172, 166, 161, 155, 149, 144, 139, 134, 129, 124, 120,
117, 114, 111, 109, 108, 107, 107, 108, 109, 111, 113, 116, 119, 123, 127, 132,
136, 141, 146, 152, 157, 162, 167, 172, 177, 181, 185, 189, 193, 196, 199, 201,
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

#endif /* RS_H_ */
