wgd-modular/utf-8-samplified/firmware/beatbox/CH.h

#ifndef CH_H_
#define CH_H_
 
const uint16_t CHLen = 1276; 
const uint8_t  CH[1276] PROGMEM = {127, 127, 121, 116, 119, 120, 114, 118, 132,
123, 119, 118, 107, 94, 93, 108, 112, 105, 89, 110, 105, 83, 104, 105, 89, 112,
114, 98, 91, 103, 120, 124, 108, 124, 139, 114, 152, 126, 152, 144, 133, 153,
128, 138, 178, 132, 139, 175, 127, 154, 197, 133, 152, 165, 154, 157, 150, 174,
90, 184, 132, 142, 165, 143, 145, 126, 158, 144, 115, 149, 109, 155, 131, 120,
142, 93, 158, 112, 143, 96, 155, 61, 156, 119, 87, 152, 102, 106, 122, 131, 75,
127, 87, 139, 124, 65, 151, 56, 133, 144, 33, 189, 51, 84, 152, 106, 87, 120,
102, 115, 102, 90, 122, 106, 61, 170, 45, 138, 102, 44, 207, 17, 132, 144, 63,
113, 185, 1, 157, 101, 96, 136, 115, 80, 166, 107, 86, 196, 97, 113, 162, 129,
108, 194, 64, 221, 78, 169, 144, 161, 142, 133, 160, 129, 187, 132, 155, 149,
145, 138, 163, 129, 151, 121, 165, 128, 169, 120, 166, 131, 155, 126, 100, 167,
120, 121, 166, 73, 173, 142, 73, 153, 158, 124, 70, 209, 86, 169, 114, 100, 133,
141, 110, 166, 93, 126, 129, 140, 186, 56, 174, 119, 125, 135, 197, 77, 122,
166, 129, 165, 116, 78, 194, 122, 84, 178, 152, 100, 130, 198, 82, 173, 115,
120, 150, 107, 151, 143, 126, 104, 131, 143, 122, 148, 135, 149, 109, 140, 158,
132, 156, 120, 129, 151, 126, 132, 159, 152, 140, 120, 185, 148, 174, 114, 150,
160, 117, 152, 140, 154, 146, 123, 146, 178, 124, 153, 123, 128, 141, 158, 128,
132, 153, 105, 146, 150, 131, 142, 134, 127, 132, 131, 145, 145, 136, 128, 120,
151, 121, 133, 145, 125, 132, 129, 143, 133, 150, 129, 117, 154, 133, 120, 153,
113, 142, 110, 116, 139, 136, 125, 97, 144, 109, 137, 117, 132, 127, 121, 124,
118, 131, 119, 131, 118, 129, 116, 124, 118, 124, 127, 110, 121, 114, 129, 133,
126, 129, 137, 130, 122, 143, 123, 123, 127, 128, 128, 134, 140, 132, 136, 137,
142, 148, 136, 129, 146, 137, 132, 127, 143, 136, 129, 133, 131, 137, 132, 125,
140, 134, 132, 128, 133, 127, 130, 132, 114, 137, 119, 126, 126, 122, 127, 126,
124, 117, 130, 121, 113, 127, 116, 122, 122, 137, 122, 124, 128, 119, 132, 121,
125, 121, 123, 114, 122, 126, 114, 122, 121, 112, 118, 110, 123, 119, 123, 116,
126, 117, 123, 119, 116, 121, 108, 124, 107, 125, 112, 116, 116, 119, 108, 128,
124, 111, 131, 111, 119, 125, 118, 118, 118, 120, 128, 113, 129, 126, 124, 128,
127, 128, 120, 130, 117, 127, 129, 124, 131, 114, 123, 118, 106, 125, 104, 116,
121, 103, 122, 115, 114, 111, 114, 111, 116, 109, 108, 110, 110, 110, 105, 107,
106, 107, 101, 109, 101, 114, 107, 108, 118, 110, 103, 116, 111, 105, 115, 106,
111, 110, 112, 111, 112, 117, 120, 115, 120, 113, 118, 120, 112, 125, 118, 122,
118, 123, 121, 119, 124, 112, 129, 111, 120, 128, 116, 124, 116, 122, 122, 117,
124, 115, 124, 123, 121, 129, 120, 125, 120, 123, 120, 123, 130, 122, 126, 129,
120, 135, 124, 125, 132, 125, 127, 129, 128, 124, 123, 125, 132, 120, 131, 126,
129, 124, 125, 129, 123, 126, 123, 127, 120, 124, 125, 117, 118, 114, 114, 126,
117, 117, 124, 120, 121, 121, 120, 117, 119, 119, 114, 122, 118, 119, 120, 118,
123, 119, 122, 117, 121, 126, 122, 124, 128, 120, 126, 124, 122, 128, 122, 128,
125, 132, 124, 132, 135, 127, 137, 129, 132, 129, 129, 128, 130, 131, 127, 131,
130, 133, 129, 137, 133, 129, 138, 128, 135, 132, 131, 133, 129, 132, 132, 133,
128, 128, 133, 132, 134, 128, 131, 134, 130, 133, 127, 130, 129, 134, 132, 134,
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

#endif /* CH_H_ */
