wgd-modular/utf-8-samplified/firmware/beatbox/RD.h

#ifndef RD_H_
#define RD_H_
 
const uint16_t RDLen = 1727; 
const uint8_t  RD[1727] PROGMEM = {131, 128, 130, 131, 123, 133, 115, 144, 121,
131, 120, 119, 153, 113, 125, 151, 113, 110, 157, 118, 109, 163, 120, 108, 134,
133, 120, 137, 127, 130, 137, 104, 137, 141, 116, 121, 156, 106, 122, 145, 114,
134, 133, 116, 132, 141, 115, 133, 125, 132, 133, 119, 137, 125, 124, 122, 143,
118, 124, 142, 99, 148, 134, 116, 134, 138, 113, 132, 147, 96, 150, 136, 104,
132, 134, 129, 120, 144, 114, 126, 140, 120, 123, 130, 133, 120, 141, 125, 123,
136, 122, 126, 132, 127, 120, 135, 135, 114, 128, 143, 117, 127, 135, 129, 128,
118, 139, 124, 129, 130, 129, 125, 136, 110, 129, 144, 118, 140, 130, 107, 144,
131, 105, 158, 123, 109, 130, 145, 110, 142, 130, 120, 141, 109, 123, 149, 137,
82, 183, 120, 74, 175, 114, 130, 130, 130, 123, 129, 131, 113, 144, 117, 131,
143, 105, 136, 138, 129, 122, 127, 147, 103, 136, 152, 102, 116, 160, 103, 117,
149, 128, 112, 137, 119, 138, 135, 120, 138, 125, 130, 131, 120, 109, 158, 132,
123, 113, 150, 125, 115, 126, 127, 120, 132, 125, 135, 121, 128, 141, 110, 151,
131, 129, 92, 181, 115, 85, 163, 147, 78, 149, 164, 63, 137, 150, 135, 97, 153,
127, 126, 126, 120, 156, 95, 141, 156, 95, 113, 156, 136, 101, 155, 119, 122,
145, 103, 134, 136, 125, 108, 153, 109, 139, 153, 104, 124, 142, 136, 93, 145,
137, 118, 136, 114, 144, 131, 95, 163, 134, 96, 131, 158, 109, 100, 172, 124,
88, 174, 110, 121, 155, 88, 151, 134, 113, 132, 134, 111, 159, 111, 104, 151,
133, 120, 124, 133, 133, 129, 92, 156, 170, 75, 114, 199, 86, 75, 195, 143, 78,
131, 158, 137, 78, 154, 162, 97, 105, 176, 123, 81, 159, 118, 129, 125, 138,
114, 150, 122, 114, 144, 121, 126, 123, 166, 80, 143, 140, 119, 139, 101, 156,
126, 122, 119, 147, 114, 106, 166, 108, 118, 156, 101, 122, 154, 109, 126, 162,
124, 93, 173, 111, 94, 158, 133, 101, 155, 125, 106, 156, 106, 136, 128, 133,
95, 179, 114, 112, 154, 108, 112, 151, 121, 108, 176, 91, 119, 160, 125, 95,
165, 122, 95, 165, 131, 89, 146, 139, 117, 109, 168, 112, 127, 134, 118, 146,
120, 107, 163, 111, 78, 188, 144, 61, 162, 157, 78, 142, 126, 163, 87, 128, 120,
207, 79, 72, 243, 98, 29, 212, 142, 69, 157, 122, 133, 128, 121, 110, 166, 95,
154, 108, 136, 142, 106, 136, 142, 94, 151, 144, 97, 150, 129, 146, 75, 159,
148, 78, 152, 133, 123, 132, 133, 106, 113, 169, 121, 126, 117, 141, 113, 133,
128, 119, 160, 93, 155, 124, 109, 142, 111, 148, 107, 149, 128, 111, 143, 118,
123, 140, 132, 115, 146, 103, 130, 162, 99, 122, 167, 102, 112, 165, 111, 109,
160, 91, 159, 110, 110, 161, 115, 121, 145, 127, 118, 133, 107, 153, 121, 127,
121, 127, 135, 143, 123, 127, 142, 115, 102, 172, 109, 112, 156, 96, 141, 110,
180, 66, 159, 157, 55, 186, 113, 138, 97, 144, 134, 127, 106, 149, 137, 111,
139, 113, 174, 72, 159, 132, 105, 168, 94, 143, 119, 125, 155, 90, 130, 119,
155, 114, 118, 153, 125, 111, 125, 151, 124, 116, 152, 115, 120, 144, 108, 155,
105, 121, 129, 158, 82, 163, 129, 93, 164, 129, 93, 155, 118, 121, 155, 129,
120, 100, 162, 91, 144, 115, 199, 55, 127, 194, 50, 151, 177, 73, 120, 172, 95,
125, 159, 136, 60, 192, 127, 58, 203, 122, 94, 130, 169, 109, 87, 184, 99, 105,
169, 136, 70, 189, 97, 119, 147, 131, 107, 157, 133, 69, 189, 94, 138, 120, 144,
110, 117, 170, 138, 77, 167, 120, 112, 138, 121, 148, 82, 161, 115, 146, 102,
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

#endif /* RD_H_ */
