wgd-modular/utf-8-samplified/firmware/808/CH.h

#ifndef CH_H_
#define CH_H_
 
const uint16_t CHLen = 939; 

const uint8_t  CH[939] PROGMEM = {124, 130, 104, 163, 118, 145, 97, 161, 98,
128, 179, 36, 192, 98, 210, 1, 225, 81, 132, 169, 39, 249, 29, 175, 123, 107,
147, 95, 186, 127, 45, 205, 95, 173, 62, 168, 125, 111, 148, 94, 191, 46, 202,
90, 130, 151, 82, 184, 93, 130, 124, 155, 91, 158, 118, 99, 167, 123, 116, 146,
107, 136, 176, 26, 212, 59, 206, 70, 157, 120, 99, 192, 70, 185, 63, 181, 98,
119, 156, 109, 118, 178, 74, 162, 100, 142, 152, 70, 183, 104, 150, 92, 146,
120, 150, 120, 113, 134, 136, 120, 119, 172, 59, 202, 59, 176, 117, 116, 128,
129, 165, 63, 181, 98, 139, 128, 133, 109, 162, 83, 160, 126, 125, 122, 141, 96,
159, 141, 75, 183, 80, 167, 120, 116, 112, 182, 66, 167, 130, 93, 169, 101, 136,
135, 112, 138, 137, 108, 145, 115, 148, 97, 157, 111, 121, 150, 122, 129, 109,
156, 110, 134, 131, 102, 170, 103, 132, 121, 135, 140, 108, 139, 111, 145, 145,
97, 144, 114, 134, 134, 119, 135, 116, 153, 91, 173, 87, 145, 136, 106, 155, 93,
156, 135, 99, 148, 114, 144, 118, 134, 127, 111, 163, 92, 153, 121, 120, 134,
138, 112, 128, 136, 131, 121, 139, 111, 127, 149, 100, 154, 120, 123, 137, 115,
122, 149, 135, 93, 153, 115, 136, 133, 115, 139, 120, 132, 125, 130, 115, 161,
99, 125, 153, 102, 148, 110, 140, 137, 99, 156, 110, 148, 103, 137, 136, 122,
129, 135, 117, 126, 136, 126, 134, 118, 136, 113, 158, 85, 170, 100, 143, 116,
137, 126, 118, 147, 110, 140, 113, 157, 96, 150, 115, 135, 124, 129, 123, 139,
118, 131, 132, 118, 143, 115, 135, 127, 128, 124, 139, 119, 133, 124, 124, 132,
136, 122, 117, 151, 107, 138, 126, 122, 142, 105, 154, 115, 128, 127, 129, 132,
125, 131, 122, 126, 142, 113, 136, 126, 125, 136, 116, 145, 105, 155, 102, 151,
112, 130, 142, 109, 138, 125, 127, 130, 126, 124, 138, 115, 140, 119, 137, 109,
154, 106, 143, 123, 118, 146, 110, 144, 114, 138, 119, 138, 118, 137, 123, 124,
144, 109, 133, 133, 123, 131, 131, 121, 133, 127, 132, 116, 143, 117, 131, 133,
116, 145, 114, 136, 119, 139, 121, 130, 126, 127, 135, 120, 131, 131, 119, 138,
123, 124, 136, 123, 132, 123, 138, 114, 134, 131, 120, 136, 124, 129, 129, 123,
135, 123, 134, 123, 126, 134, 121, 134, 129, 122, 131, 128, 128, 127, 128, 128,
129, 126, 129, 127, 129, 129, 126, 125, 133, 131, 118, 135, 125, 129, 126, 130,
128, 124, 129, 137, 114, 139, 121, 131, 132, 119, 135, 127, 125, 131, 129, 120,
137, 122, 136, 120, 129, 128, 132, 122, 134, 125, 124, 134, 125, 126, 127, 135,
119, 136, 120, 136, 122, 132, 126, 128, 130, 125, 131, 126, 129, 129, 129, 122,
135, 124, 131, 123, 134, 124, 132, 124, 131, 130, 122, 133, 125, 130, 125, 134,
120, 136, 121, 132, 128, 124, 134, 120, 135, 125, 126, 135, 122, 129, 132, 122,
134, 123, 132, 125, 131, 126, 125, 138, 117, 136, 124, 128, 133, 122, 131, 128,
125, 131, 124, 131, 124, 130, 129, 124, 135, 118, 137, 125, 124, 133, 124, 130,
127, 130, 124, 132, 125, 127, 131, 126, 128, 129, 127, 126, 133, 121, 134, 125,
128, 129, 128, 125, 132, 124, 131, 126, 128, 131, 124, 134, 121, 134, 122, 133,
124, 130, 126, 129, 129, 128, 125, 132, 128, 125, 132, 124, 132, 125, 130, 126,
130, 125, 131, 126, 129, 127, 128, 129, 128, 128, 127, 130, 126, 130, 127, 128,
128, 132, 123, 131, 127, 127, 131, 126, 128, 127, 132, 123, 132, 126, 129, 128,
128, 128, 129, 127, 129, 128, 127, 129, 126, 131, 126, 130, 126, 129, 127, 129,
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

#endif /* CH_H_ */
