wgd-modular/utf-8-samplified/firmware/808/CL.h

#ifndef CL_H_
#define CL_H_

const uint16_t CLLen = 1022; 
const uint8_t CL[1022] PROGMEM = {131, 123, 174, 125, 47, 134, 201, 135, 53,
117, 199, 147, 59, 104, 192, 159, 68, 92, 184, 168, 78, 83, 173, 176, 89, 77,
162, 181, 100, 73, 150, 184, 112, 71, 138, 184, 123, 72, 127, 183, 134, 75, 117,
179, 144, 80, 108, 173, 152, 86, 100, 167, 159, 93, 94, 159, 164, 101, 90, 151,
168, 110, 87, 142, 169, 118, 87, 133, 169, 127, 88, 125, 167, 134, 90, 118, 164,
141, 94, 112, 160, 147, 99, 106, 155, 152, 104, 102, 149, 155, 110, 100, 143,
157, 116, 98, 137, 158, 123, 98, 130, 158, 129, 99, 125, 156, 134, 101, 119,
154, 139, 104, 115, 150, 143, 108, 111, 146, 146, 112, 109, 142, 148, 116, 107,
138, 149, 121, 106, 133, 150, 125, 106, 129, 149, 129, 107, 125, 148, 133, 109,
121, 146, 137, 111, 118, 143, 139, 114, 115, 141, 142, 117, 114, 137, 143, 120,
113, 134, 144, 124, 112, 131, 144, 127, 112, 128, 143, 130, 113, 125, 142, 132,
115, 122, 141, 135, 116, 120, 139, 137, 118, 119, 136, 138, 121, 117, 134, 139,
123, 117, 132, 139, 125, 117, 129, 139, 128, 117, 127, 139, 130, 118, 125, 138,
132, 119, 124, 137, 133, 120, 122, 135, 134, 122, 121, 134, 135, 123, 120, 132,
136, 125, 120, 130, 136, 127, 120, 129, 136, 128, 120, 127, 135, 130, 121, 126,
135, 131, 122, 125, 134, 132, 123, 124, 133, 133, 124, 123, 132, 133, 125, 122,
130, 134, 126, 122, 129, 134, 127, 122, 128, 134, 128, 123, 127, 133, 129, 123,
126, 133, 130, 124, 125, 132, 131, 124, 125, 131, 132, 125, 124, 130, 132, 126,
124, 130, 132, 127, 124, 129, 132, 128, 124, 128, 132, 128, 124, 127, 132, 129,
125, 126, 131, 130, 125, 126, 131, 130, 125, 126, 130, 131, 126, 125, 130, 131,
127, 125, 129, 131, 127, 125, 128, 131, 128, 125, 128, 131, 128, 126, 128, 130,
129, 127, 128, 129, 129, 127, 128, 129, 128, 128, 128, 128, 128, 128, 128, 128,
128, 128, 128, 128, 128, 128, 128, 128, 128, 128, 128, 128, 128, 128, 128, 128,
128, 128, 128, 128, 128, 128, 128, 128, 128, 128, 128, 128, 128, 128, 128, 128,
128, 128, 128, 128, 128, 128, 128, 128, 128, 128, 128, 128, 128, 128, 128, 128,
128, 128, 128, 128, 128, 128, 128, 128, 128, 128, 128, 128, 128, 128, 128, 128,
128, 128, 128, 128, 128, 128, 128, 128, 128, 128, 128, 128, 128, 128, 128, 128,
128, 128, 128, 128, 128, 128, 128, 128, 128, 128, 128, 128, 128, 128, 128, 128,
128, 128, 128, 128, 128, 128, 128, 128, 128, 128, 128, 128, 128, 128, 128, 128,
128, 128, 128, 128, 128, 128, 128, 128, 128, 128, 128, 128, 128, 128, 128, 128,
128, 128, 128, 128, 128, 128, 128, 128, 128, 128, 128, 128, 128, 128, 128, 128,
128, 128, 128, 128, 128, 128, 128, 128, 128, 128, 128, 128, 128, 128, 128, 128,
128, 128, 128, 128, 128, 128, 128, 128, 128, 128, 128, 128, 128, 128, 128, 128,
128, 128, 128, 128, 128, 128, 128, 128, 128, 128, 128, 128, 128, 128, 128, 128,
128, 128, 128, 128, 128, 128, 128, 128, 128, 128, 128, 128, 128, 128, 128, 128,
128, 128, 128, 128, 128, 128, 128, 128, 128, 128, 128, 128, 128, 128, 128, 128,
128, 128, 128, 128, 128, 128, 128, 128, 128, 128, 128, 128, 128, 128, 128, 128,
128, 128, 128, 128, 128, 128, 128, 128, 128, 128, 128, 128, 128, 128, 128, 128,
128, 128, 128, 128, 128, 128, 128, 128, 128, 128, 128, 128, 128, 128, 128, 128,
128, 128, 128, 128, 128, 128, 128, 128, 128, 128, 128, 128, 128, 128, 128, 128,
128, 128, 128, 128, 128, 128, 128, 128, 128, 128, 128, 128, 128, 128, 128, 128,
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

#endif /* CL.WAV_H_ */
