wgd-modular/utf-8-samplified/firmware/808/CR.h

#ifndef CR_H_
#define CR_H_

const uint16_t CRLen = 1019; 
const uint8_t CR[1019] PROGMEM = {128, 128, 128, 128, 128, 128, 128, 128,
128, 128, 128, 128, 127, 129, 128, 127, 129, 128, 128, 128, 128, 128, 128, 127,
129, 129, 127, 128, 128, 128, 129, 127, 129, 128, 129, 127, 130, 127, 127, 130,
128, 127, 127, 130, 127, 130, 125, 130, 126, 130, 127, 129, 129, 127, 127, 129,
130, 127, 128, 127, 130, 126, 130, 125, 131, 127, 129, 126, 131, 127, 126, 131,
128, 125, 130, 128, 127, 130, 127, 131, 123, 131, 129, 128, 121, 136, 124, 132,
126, 129, 127, 127, 132, 121, 136, 120, 134, 126, 130, 125, 130, 130, 125, 129,
129, 129, 126, 132, 123, 131, 132, 121, 134, 127, 124, 137, 115, 137, 127, 126,
130, 125, 134, 117, 136, 127, 131, 122, 132, 127, 123, 139, 118, 133, 124, 132,
127, 127, 129, 130, 126, 126, 134, 126, 123, 129, 133, 127, 133, 116, 136, 127,
127, 130, 126, 129, 130, 125, 132, 128, 119, 137, 124, 132, 125, 126, 129, 131,
127, 121, 134, 127, 126, 136, 118, 130, 133, 125, 129, 127, 129, 132, 126, 123,
133, 124, 132, 125, 132, 126, 126, 130, 129, 131, 122, 131, 130, 125, 129, 134,
122, 126, 131, 128, 129, 126, 130, 126, 130, 128, 125, 129, 126, 134, 122, 129,
132, 121, 131, 128, 129, 128, 125, 131, 128, 128, 128, 125, 131, 127, 125, 133,
124, 130, 127, 125, 132, 125, 130, 125, 131, 125, 128, 130, 126, 130, 126, 129,
127, 128, 129, 128, 127, 127, 128, 130, 126, 127, 129, 127, 129, 125, 129, 128,
128, 128, 128, 127, 127, 130, 126, 129, 127, 128, 128, 128, 128, 128, 128, 128,
128, 127, 128, 128, 128, 128, 128, 127, 129, 127, 128, 128, 128, 128, 128, 128,
128, 128, 128, 128, 128, 128, 128, 128, 128, 128, 128, 128, 128, 128, 128, 128,
128, 128, 128, 128, 128, 128, 128, 128, 128, 128, 128, 128, 128, 128, 128, 128,
128, 128, 128, 128, 128, 128, 128, 128, 128, 128, 128, 128, 128, 128, 128, 128,
128, 128, 128, 128, 128, 128, 128, 128, 128, 128, 128, 128, 128, 128, 128, 128,
128, 128, 128, 128, 128, 128, 128, 128, 128, 128, 128, 128, 128, 128, 128, 128,
128, 128, 128, 128, 128, 128, 128, 128, 128, 128, 128, 128, 128, 128, 128, 128,
128, 128, 128, 128, 128, 128, 128, 128, 128, 128, 128, 128, 128, 128, 128, 128,
128, 128, 128, 128, 128, 128, 128, 128, 128, 128, 128, 128, 128, 128, 128, 128,
128, 128, 128, 128, 128, 128, 128, 128, 128, 128, 128, 128, 128, 128, 128, 128,
128, 128, 128, 128, 128, 128, 128, 128, 128, 128, 128, 128, 128, 128, 128, 128,
128, 128, 128, 128, 128, 128, 128, 128, 128, 128, 128, 128, 128, 128, 128, 128,
128, 128, 128, 128, 128, 128, 128, 128, 128, 128, 128, 128, 128, 128, 128, 128,
128, 128, 128, 128, 128, 128, 128, 128, 128, 128, 128, 128, 128, 128, 128, 128,
128, 128, 128, 128, 128, 128, 128, 128, 128, 128, 128, 128, 128, 128, 128, 128,
128, 128, 128, 128, 128, 128, 128, 128, 128, 128, 128, 128, 128, 128, 128, 128,
128, 128, 128, 128, 128, 128, 128, 128, 128, 128, 128, 128, 128, 128, 128, 128,
128, 128, 128, 128, 128, 128, 128, 128, 128, 128, 128, 128, 128, 128, 128, 128,
128, 128, 128, 128, 128, 128, 128, 128, 128, 128, 128, 128, 128, 128, 128, 128,
128, 128, 128, 128, 128, 128, 128, 128, 128, 128, 128, 128, 128, 128, 128, 128,
128, 128, 128, 128, 128, 128, 128, 128, 128, 128, 128, 128, 128, 128, 128, 128,
128, 128, 128, 128, 128, 128, 128, 128, 128, 128, 128, 128, 128, 128, 128, 128,
128, 128, 128, 128, 128, 128, 128, 128, 128, 128, 128, 128, 128, 128, 128, 128,
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

#endif /* CR.WAV_H_ */
