wgd-modular/utf-8-samplified/firmware/dilectro/CH.h

#ifndef CH_H_
#define CH_H_
 
const uint16_t CHLen = 366;

const uint8_t CH[366] PROGMEM = {127, 130, 124, 131, 127, 124, 139, 91, 109,
138, 126, 157, 149, 121, 142, 130, 128, 129, 121, 150, 160, 129, 119, 130, 123,
129, 119, 133, 114, 126, 121, 141, 103, 97, 176, 141, 122, 122, 134, 120, 131,
106, 140, 135, 121, 164, 144, 119, 129, 122, 120, 130, 121, 132, 120, 125, 124,
135, 110, 161, 147, 120, 154, 161, 160, 121, 123, 119, 125, 127, 128, 122, 122,
125, 121, 124, 126, 121, 123, 124, 126, 118, 130, 122, 122, 124, 126, 123, 123,
132, 119, 127, 124, 124, 125, 124, 122, 125, 125, 131, 116, 134, 124, 128, 129,
122, 128, 122, 133, 119, 130, 124, 127, 123, 129, 124, 130, 128, 127, 128, 125,
131, 128, 129, 124, 131, 126, 132, 123, 127, 126, 127, 123, 128, 125, 125, 131,
124, 126, 126, 127, 125, 128, 126, 127, 125, 129, 123, 126, 130, 129, 127, 128,
123, 132, 122, 130, 126, 126, 132, 122, 131, 124, 129, 126, 129, 127, 128, 126,
129, 125, 131, 125, 128, 127, 129, 127, 126, 131, 124, 131, 125, 131, 126, 130,
126, 128, 128, 129, 127, 127, 131, 125, 129, 129, 127, 129, 129, 127, 129, 128,
129, 127, 129, 128, 128, 128, 129, 126, 131, 127, 129, 128, 128, 129, 127, 130,
127, 128, 128, 130, 126, 130, 127, 129, 127, 129, 127, 130, 129, 128, 129, 128,
129, 127, 131, 126, 130, 127, 130, 127, 128, 130, 127, 129, 127, 131, 127, 130,
130, 125, 131, 129, 125, 132, 128, 129, 128, 129, 129, 128, 129, 128, 128, 129,
129, 127, 131, 127, 129, 129, 127, 129, 129, 129, 126, 129, 129, 128, 129, 129,
128, 129, 128, 129, 128, 130, 128, 129, 129, 128, 129, 128, 129, 128, 128, 129,
128, 129, 129, 128, 129, 128, 129, 128, 129, 129, 128, 128, 128, 128, 128, 129,
127, 129, 128, 128, 129, 128, 129, 128, 128, 129, 128, 129, 128, 129, 128, 129,
128, 129, 128, 128, 129, 128, 129, 128, 129, 128, 129, 128, 129, 127, 129, 128,
128, 128, 128, 128, 128, 129, 128, 128, 128, 129, 127, 130, 127, 129, 128, 129,
129, 127, 129, 128, 129, };

#endif /* CH_H_ */
