wgd-modular/utf-8-samplified/firmware/dilectro/CL.h

#ifndef CL_H_
#define CL_H_
 
const uint16_t CLLen = 469;

const uint8_t CL[469] PROGMEM = {127, 129, 127, 129, 126, 188, 180, 145, 103,
25, 48, 67, 96, 144, 174, 139, 187, 190, 171, 156, 96, 65, 67, 104, 72, 165,
175, 167, 172, 157, 144, 90, 75, 68, 119, 129, 183, 173, 149, 143, 111, 108,
119, 142, 116, 108, 132, 143, 135, 151, 113, 109, 126, 115, 121, 142, 152, 143,
133, 120, 121, 118, 119, 123, 133, 125, 126, 134, 150, 132, 126, 116, 124, 133,
125, 129, 123, 134, 126, 119, 124, 130, 126, 128, 130, 135, 134, 134, 131, 125,
124, 124, 123, 128, 128, 126, 125, 129, 130, 133, 129, 132, 125, 124, 121, 125,
128, 130, 134, 129, 131, 127, 133, 119, 133, 113, 145, 68, 110, 189, 114, 155,
189, 124, 83, 121, 131, 132, 102, 140, 137, 117, 93, 118, 127, 141, 178, 171,
104, 91, 81, 88, 168, 147, 201, 183, 129, 78, 85, 97, 86, 125, 148, 144, 144,
154, 130, 133, 110, 113, 141, 141, 139, 129, 125, 134, 122, 92, 114, 137, 147,
145, 110, 114, 141, 134, 115, 123, 142, 131, 118, 145, 135, 116, 118, 124, 124,
144, 124, 106, 126, 117, 123, 141, 153, 125, 128, 139, 130, 116, 111, 116, 132,
132, 122, 131, 132, 132, 123, 135, 131, 127, 123, 121, 122, 122, 130, 130, 135,
133, 130, 126, 121, 124, 121, 125, 126, 131, 128, 128, 130, 128, 123, 129, 127,
127, 129, 125, 131, 129, 135, 129, 128, 121, 125, 123, 137, 124, 132, 47, 115,
128, 55, 192, 234, 212, 109, 129, 72, 51, 91, 132, 184, 154, 139, 113, 162, 157,
139, 144, 64, 70, 105, 112, 192, 177, 165, 139, 103, 103, 82, 110, 104, 105,
165, 188, 188, 150, 99, 81, 119, 125, 125, 138, 112, 129, 120, 136, 126, 137,
179, 135, 134, 111, 111, 121, 104, 130, 135, 144, 136, 140, 119, 118, 134, 126,
136, 144, 133, 117, 117, 107, 131, 142, 142, 133, 151, 124, 99, 73, 75, 118,
150, 230, 173, 175, 172, 59, 38, 105, 152, 132, 162, 182, 148, 120, 61, 108,
131, 126, 186, 145, 103, 107, 136, 143, 92, 146, 116, 85, 149, 128, 166, 177,
195, 127, 70, 46, 17, 139, 193, 194, 217, 148, 112, 106, 94, 89, 124, 160, 157,
150, 123, 87, 70, 96, 124, 181, 165, 141, 181, 104, 77, 151, 125, 174, 109, 123,
132, 65, 99, 93, 163, 163, 116, 171, 189, 65, 111, 127, 111, 97, 125, 181, 153,
145, 156, 187, 108, 109, 59, 50, 72, 86, 212, 211, 148, 161, 124, 117, 142, 71,
119, 152, 79, 134, 174, 154, 164, 88, 61, 82, 119, 143, 191, 194, 78, 131, 123,
170, 168, 91, 88, 20, 106, 153, 148, 131, 139, 196, 187, 182, 132, 54, 124, 124,
97, 107, 102, };

#endif /* CL_H_ */
