wgd-modular/utf-8-samplified/firmware/808/RS.h

#ifndef RS_H_
#define RS_H_

const uint16_t RSLen = 201; 
const uint8_t RS[201] PROGMEM = {128, 130, 122, 125, 133, 134, 110, 73, 98,
159, 194, 166, 98, 90, 115, 152, 219, 139, 70, 102, 116, 186, 177, 158, 76, 48,
142, 149, 144, 131, 79, 67, 126, 169, 163, 112, 100, 121, 126, 178, 173, 114,
112, 119, 166, 169, 146, 130, 105, 103, 101, 99, 104, 99, 85, 110, 148, 161,
139, 134, 140, 145, 155, 160, 144, 127, 127, 143, 138, 122, 113, 104, 103, 103,
108, 113, 121, 121, 124, 135, 143, 141, 137, 137, 139, 144, 148, 144, 136, 130,
123, 116, 112, 110, 110, 113, 118, 123, 128, 132, 135, 136, 136, 136, 134, 131,
128, 129, 131, 130, 128, 126, 125, 124, 124, 124, 125, 126, 127, 128, 129, 130,
130, 130, 130, 129, 129, 129, 128, 128, 127, 127, 127, 127, 128, 128, 128, 128,
128, 128, 128, 128, 128, 128, 128, 128, 128, 128, 128, 128, 128, 128, 128, 128,
128, 128, 128, 128, 128, 128, 128, 128, 128, 128, 128, 128, 128, 128, 128, 128,
128, 128, 128, 128, 128, 128, 128, 128, 128, 128, 128, 128, 128, 128, 128, 128,
128, 128, 128, 128, 128, 128, 128, 128, 128, 128, 128, 128, 128, 128, 128, };

#endif /* RS.WAV_H_ */
